Bastardkb/Charybdis/pics/1aa.png

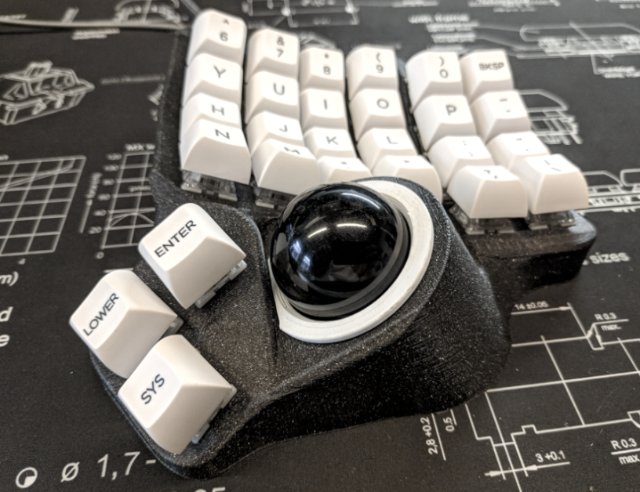
pics/1aa.png
