Bastardkb/Charybdis/pics/1ab.jpeg

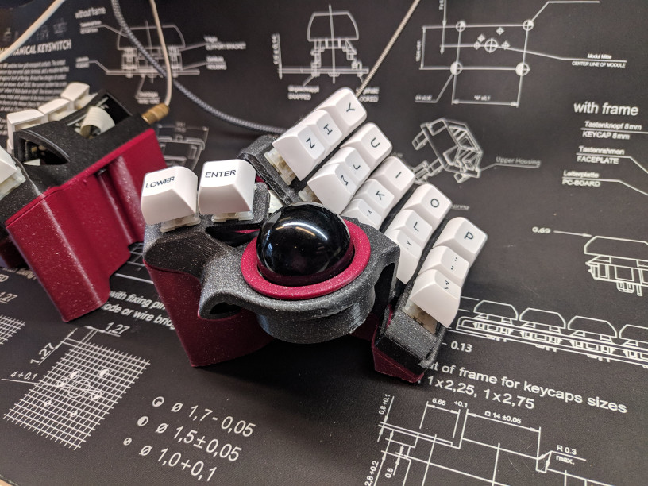
pics/1ab.jpeg
