Bastardkb/Charybdis/pics/1af.jpg

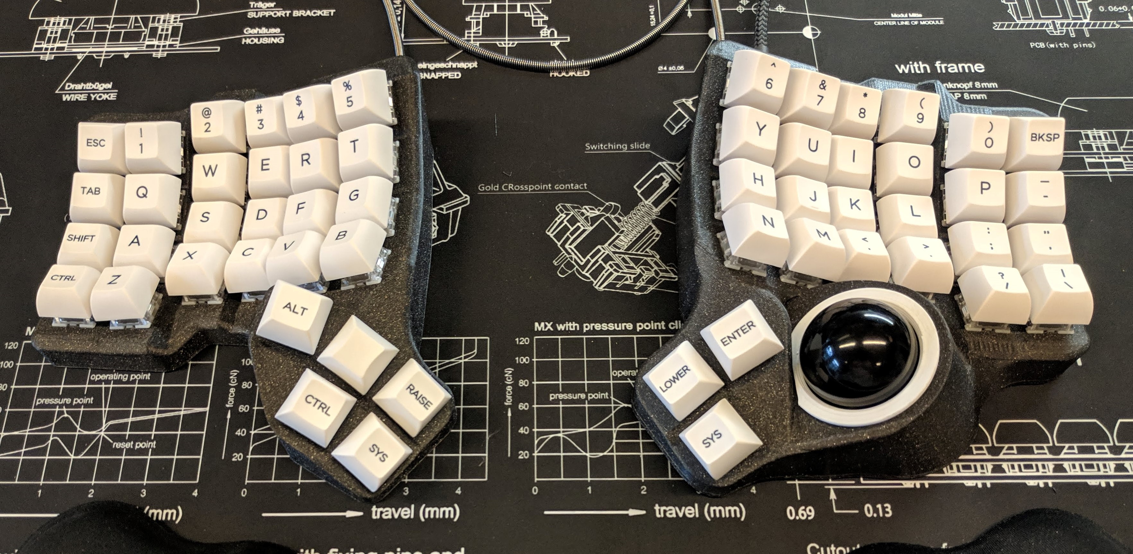
pics/1af.jpg
