Bastardkb/Charybdis/files/adapter_v4_bottom_v17.stl

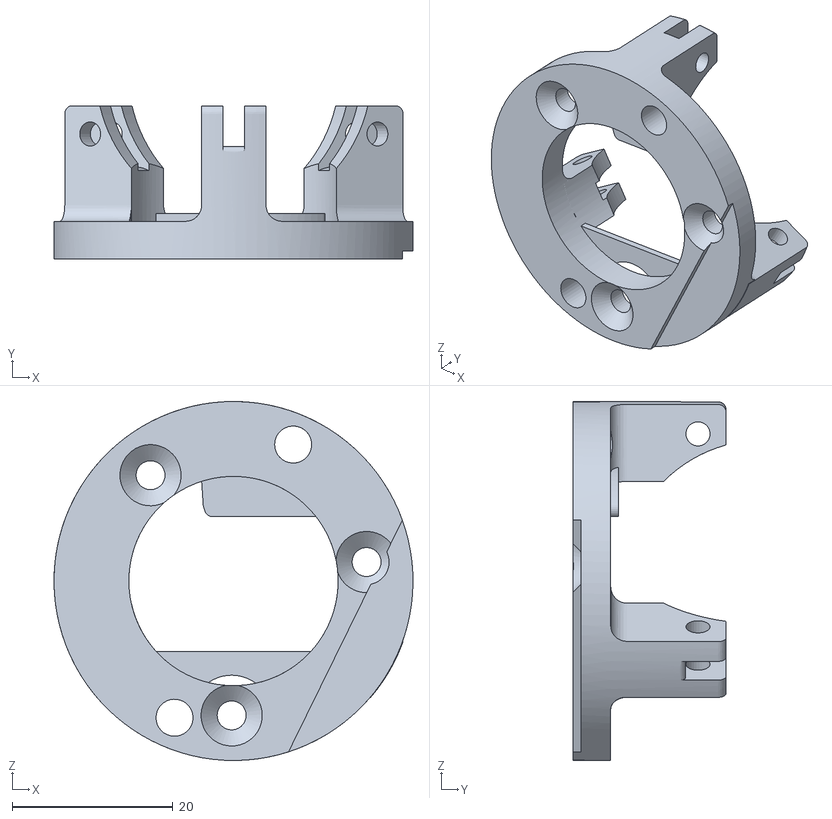
[picture p79: CAD file, 2023-07-04]
files/adapter_v4_bottom_v17.stl
44.6 x 19.1 x 44.6
