Bastardkb/Charybdis/files/mods/4x6-palm-rest-mkII/charybdis_v4_247_right_with_pads.stl

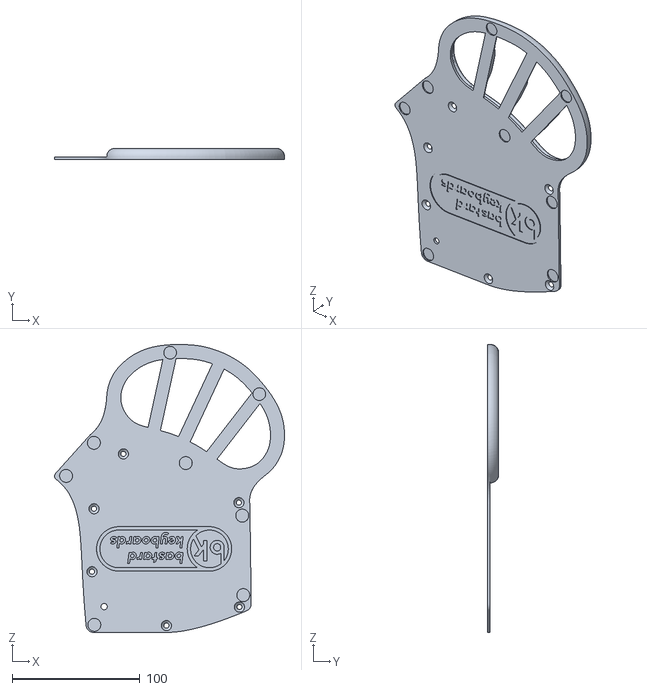
[picture p80: CAD file, 2025-02-24]
files/mods/4x6-palm-rest-mkII/charybdis_v4_247_right_with_pads.stl
180.3 x 9.00 x 225.7
