Bastardkb/Charybdis/files/mods/4x6-palm-rest/Charybdis-PlamRest-Straight.SLDPRT

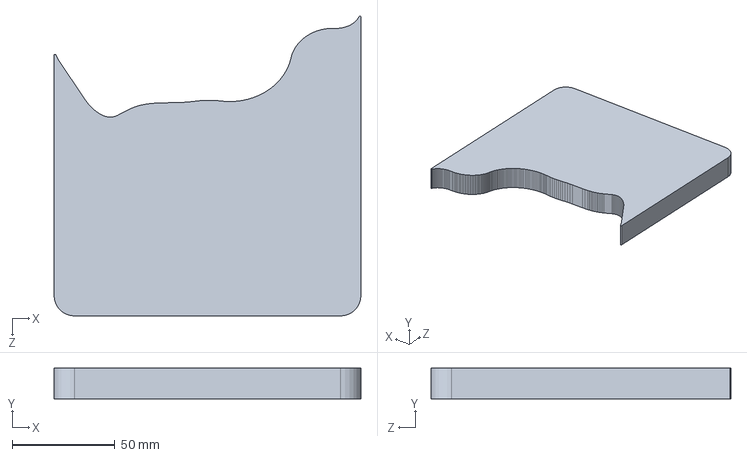
[picture p81: CAD file, 2023-12-05]
files/mods/4x6-palm-rest/Charybdis-PlamRest-Straight.SLDPRT
149.6 x 15.0 x 146.2 mm
