Bastardkb/Charybdis/files/mods/aa_3.7v_battery_holder/battery_holder_cover.stl

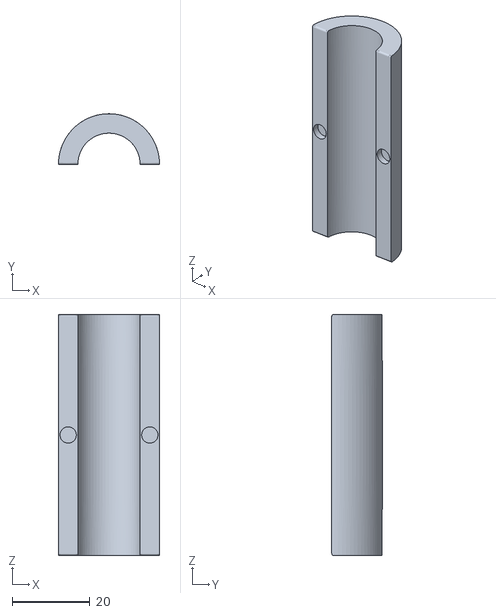
[picture p82: CAD file, 2025-08-21]
files/mods/aa_3.7v_battery_holder/battery_holder_cover.stl
26.0 x 13.0 x 62.0
