Bastardkb/Charybdis/files/mods/aa_3.7v_battery_holder/charybdis_mini/TBK_mini_v3 v29_snap_fit_with_battery.stl

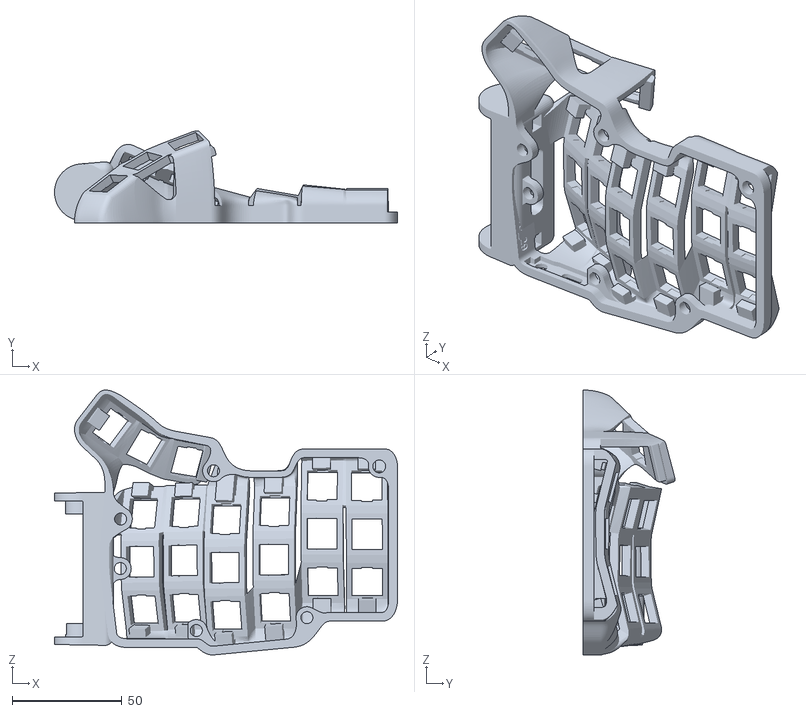
[picture p83: CAD file, 2025-08-21]
files/mods/aa_3.7v_battery_holder/charybdis_mini/TBK_mini_v3 v29_snap_fit_with_battery.stl
156.5 x 42.0 x 120.9
