Bastardkb/Charybdis/files/mods/aa_3.7v_battery_holder/charybdis_nano/charybdisnano_v2_v187_snap_fit_with_battery.stl

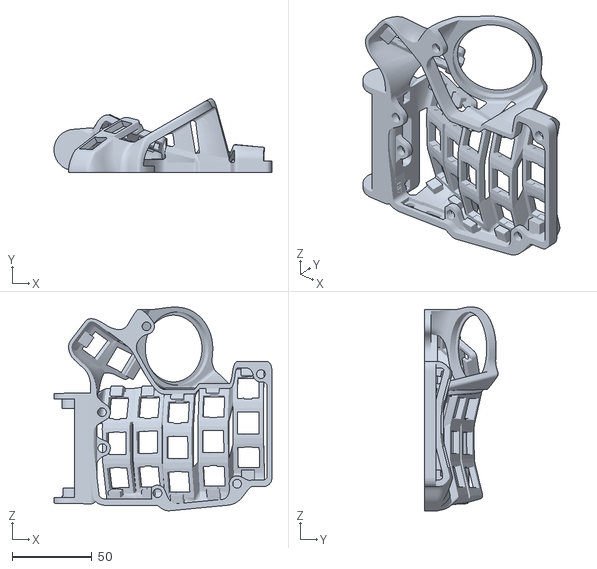
[picture p84: CAD file, 2025-08-21]
files/mods/aa_3.7v_battery_holder/charybdis_nano/charybdisnano_v2_v187_snap_fit_with_battery.stl
137.1 x 46.2 x 128.1
