Bastardkb/Charybdis/files/mods/bottom_adapter_alternative_sensors/adapter_paw3360_3389_module_20240424.stl

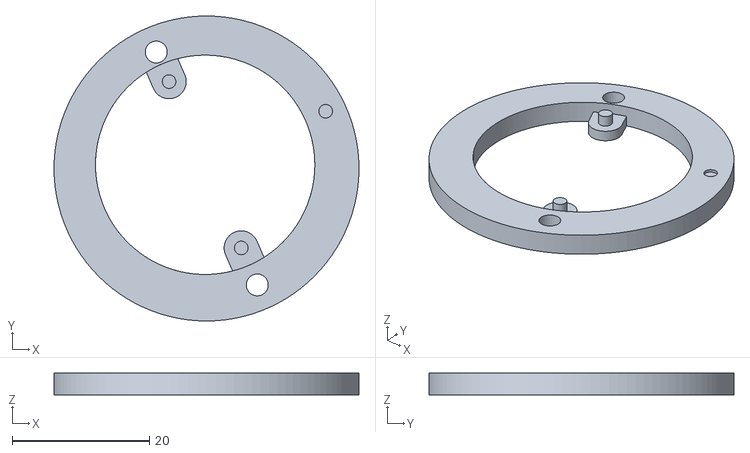
[picture p85: CAD file, 2026-08-29]
files/mods/bottom_adapter_alternative_sensors/adapter_paw3360_3389_module_20240424.stl
44.5 x 44.5 x 3.20
