Bastardkb/Charybdis/files/mods/btu/adapter_btu_bottom_v32.stl

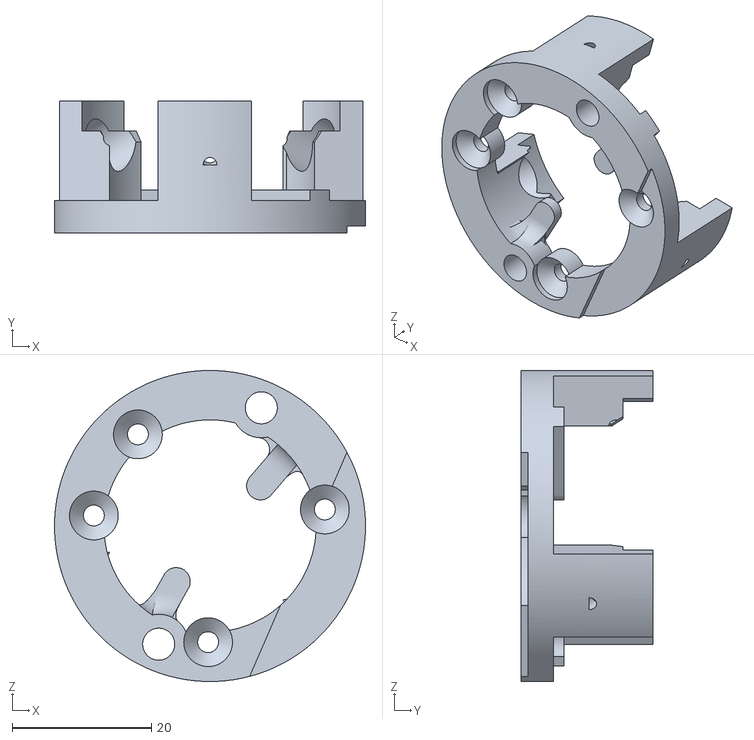
[picture p86: CAD file, 2021-10-12]
files/mods/btu/adapter_btu_bottom_v32.stl
44.7 x 19.0 x 44.7
