Bastardkb/Charybdis/files/mods/modular-thumb-cluster/mod-case.stl

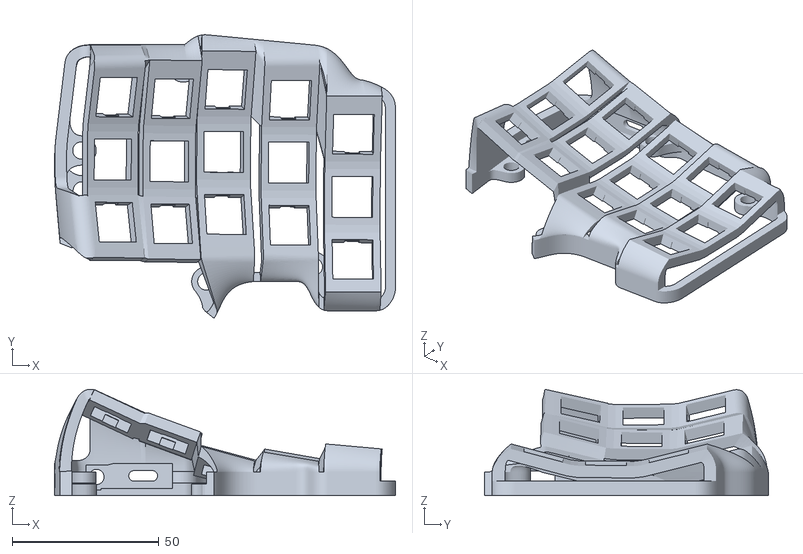
[picture p87: CAD file, 2022-09-18]
files/mods/modular-thumb-cluster/mod-case.stl
116.1 x 96.5 x 36.2
