Bastardkb/Charybdis/files/mods/pg1353_choc_v2/3x5_3_high_v2_pg1353_left.3mf

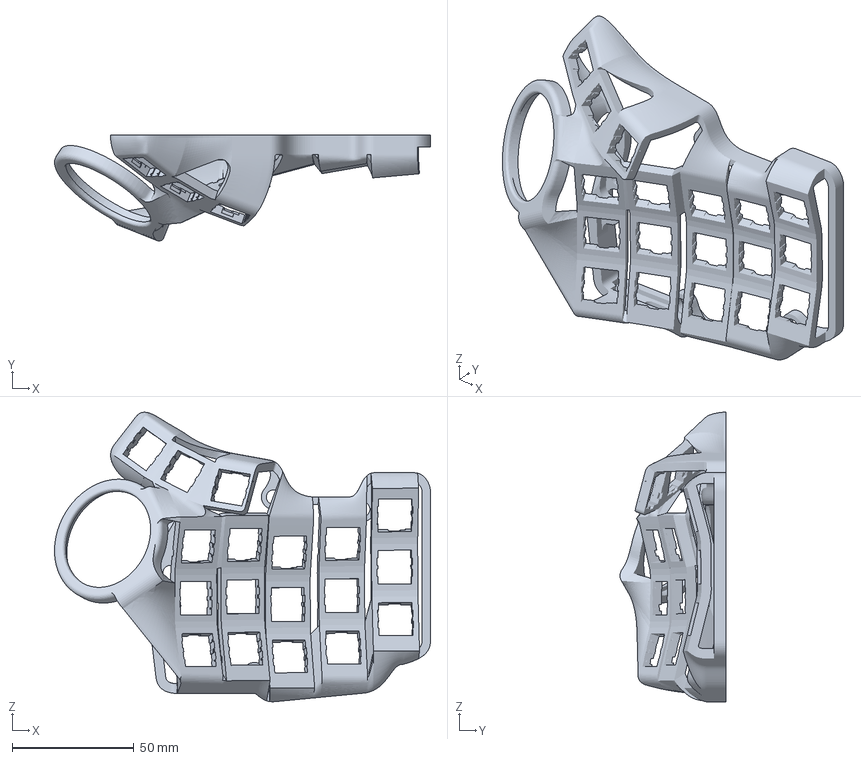
[picture p88: CAD file, 2026-08-30]
files/mods/pg1353_choc_v2/3x5_3_high_v2_pg1353_left.3mf
154.3 x 43.5 x 118.8 mm
