Bastardkb/Charybdis/files/mods/sensor_cover/Sensor_cover.stl

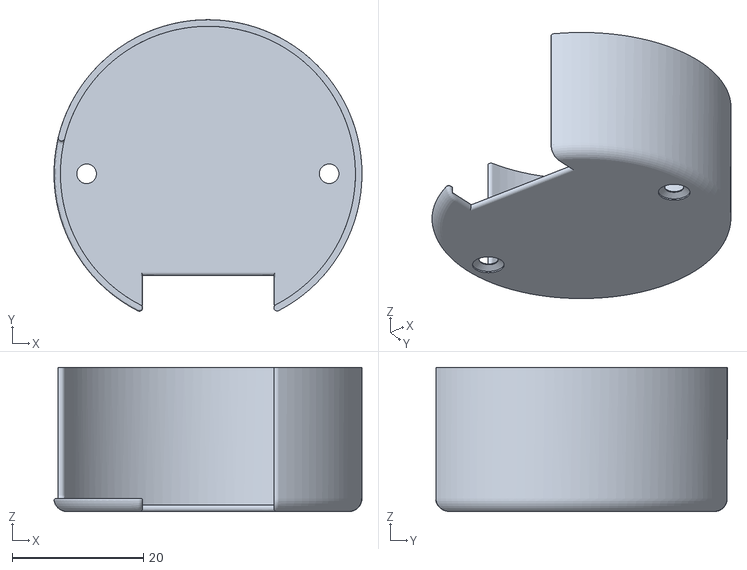
[picture p89: CAD file, 2023-04-05]
files/mods/sensor_cover/Sensor_cover.stl
47.0 x 44.5 x 22.0
