Bastardkb/Charybdis/files/mods/snapfit_pcb_case/charybdis_mini/CMini_v1_v11_snap_fit.stl

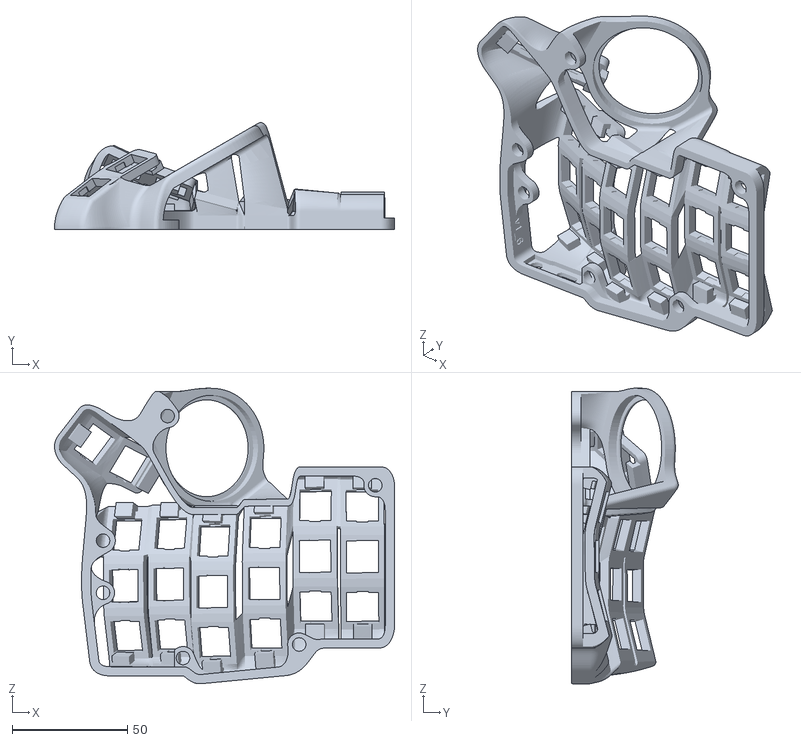
[picture p90: CAD file, 2025-08-21]
files/mods/snapfit_pcb_case/charybdis_mini/CMini_v1_v11_snap_fit.stl
147.4 x 46.2 x 128.1
