Bastardkb/Charybdis/files/mods/snapfit_pcb_case/charybdis_nano/charybdisnano_v2_v187_snap_fit.stl

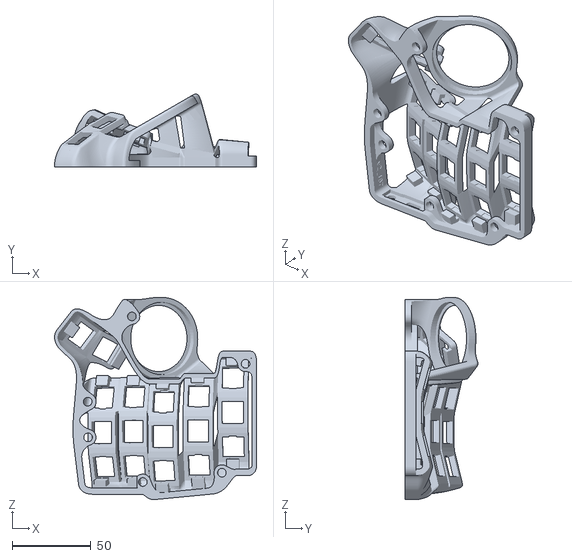
[picture p91: CAD file, 2025-08-21]
files/mods/snapfit_pcb_case/charybdis_nano/charybdisnano_v2_v187_snap_fit.stl
128.0 x 46.2 x 128.1
