Bastardkb/Charybdis/files/mods/Static-bearing-Veichu-drop-in/Static-bearing-holder_v221117.stl

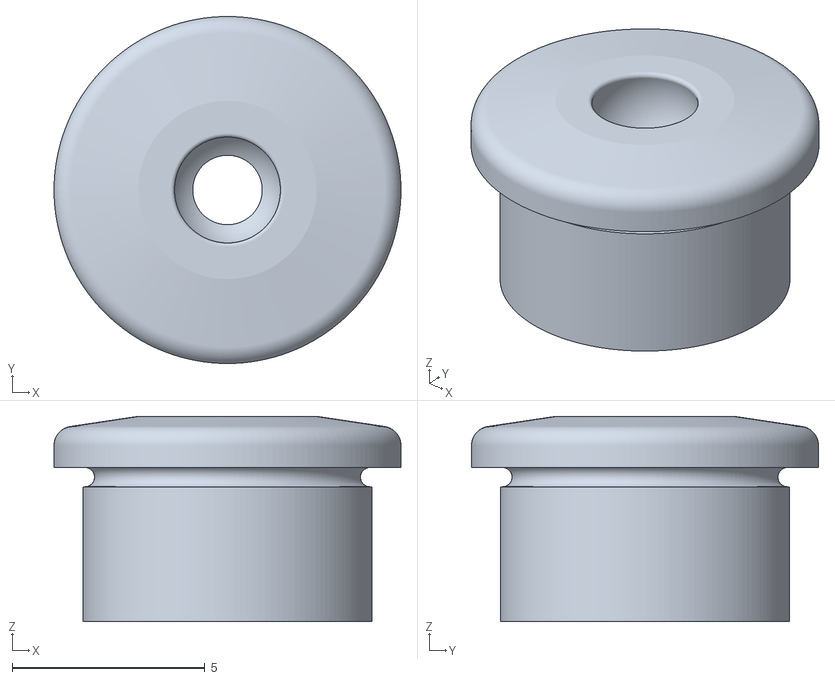
[picture p92: CAD file, 2024-09-02]
files/mods/Static-bearing-Veichu-drop-in/Static-bearing-holder_v221117.stl
9.00 x 9.00 x 5.33
