Bastardkb/Charybdis/files/mods/static-bearing/printable_btu_2.5mm_ball.stl

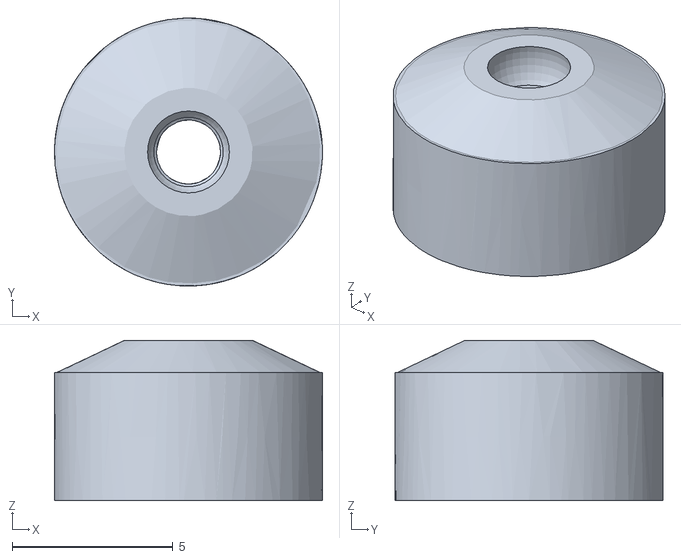
[picture p93: CAD file, 2022-09-18]
files/mods/static-bearing/printable_btu_2.5mm_ball.stl
8.35 x 8.35 x 5.00
