Bastardkb/Charybdis/files/mods/tenting-stand-with-wrist-pads/3x5+3_low_tent_plate.stl

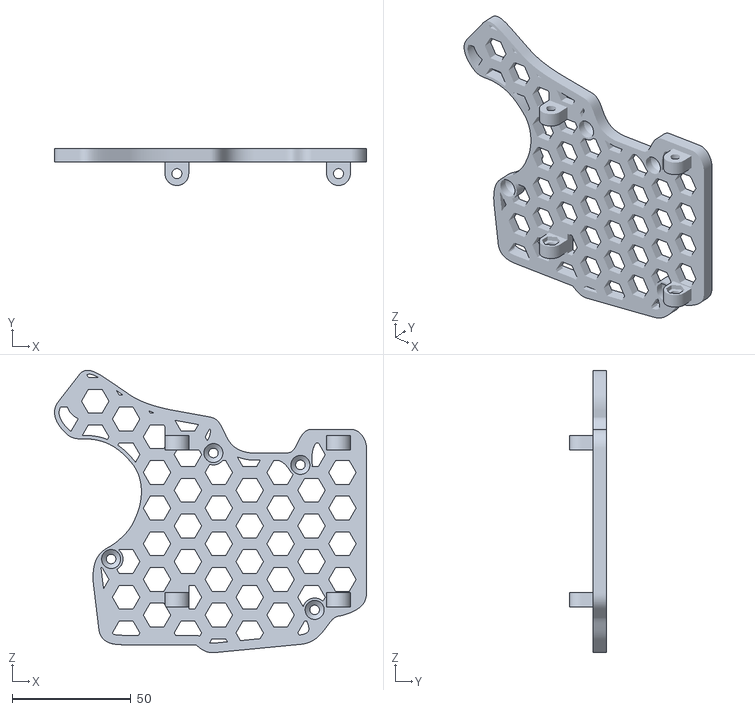
[picture p94: CAD file, 2023-08-22]
files/mods/tenting-stand-with-wrist-pads/3x5+3_low_tent_plate.stl
131.3 x 15.6 x 118.8
