Bastardkb/Charybdis/files/mods/tenting-stand-with-wrist-pads/wrist-pad-variant-parts/pads-base-short.stl

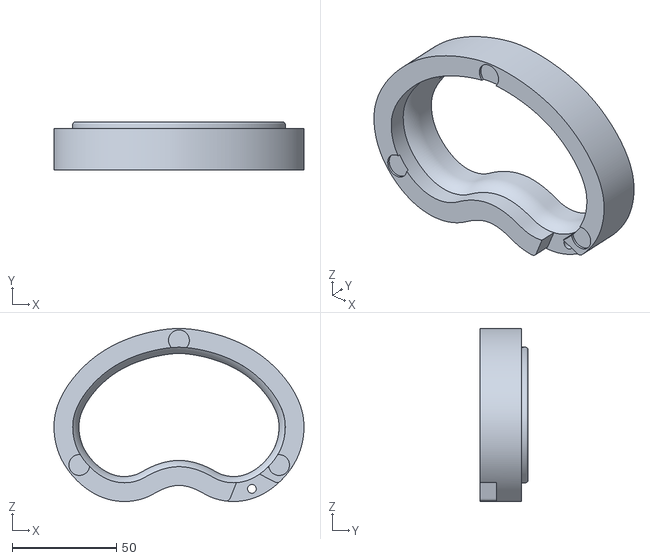
[picture p95: CAD file, 2023-08-22]
files/mods/tenting-stand-with-wrist-pads/wrist-pad-variant-parts/pads-base-short.stl
120.0 x 23.0 x 83.1
