Bastardkb/Charybdis/files/mods/trackball_retainer/3x5/Ball_cover_resin_5mm.stl

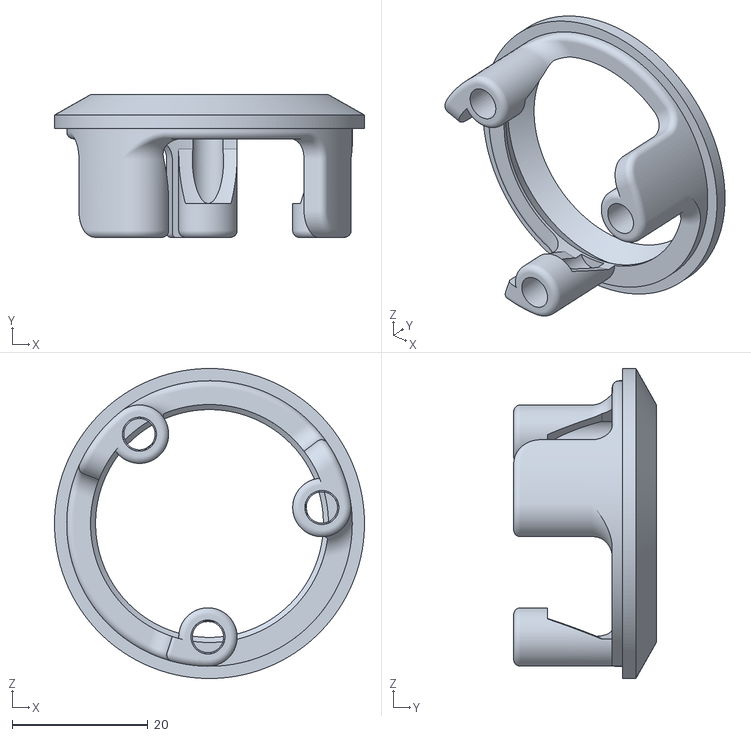
[picture p96: CAD file, 2024-01-04]
files/mods/trackball_retainer/3x5/Ball_cover_resin_5mm.stl
45.6 x 21.0 x 45.6
