Bastardkb/Charybdis/files/mods/trackball_retainer/4x6/trackball_retainer.stl

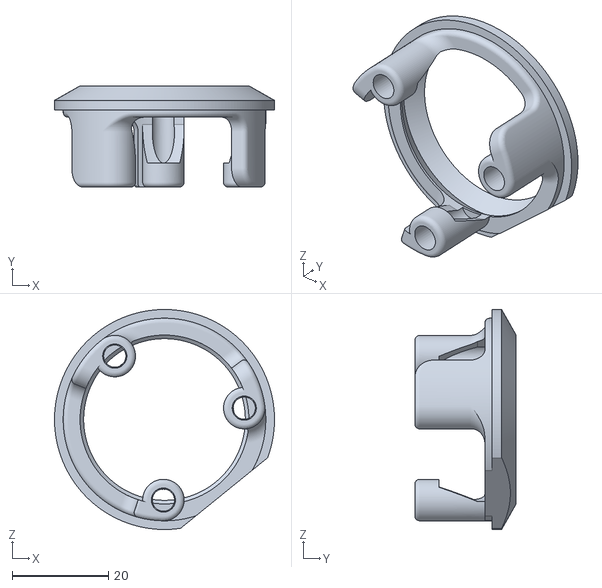
[picture p97: CAD file, 2025-02-24]
files/mods/trackball_retainer/4x6/trackball_retainer.stl
45.6 x 21.0 x 45.6
