Bastardkb/Charybdis/files/mods/trackpad/3x5-tent/tent-connector.stl

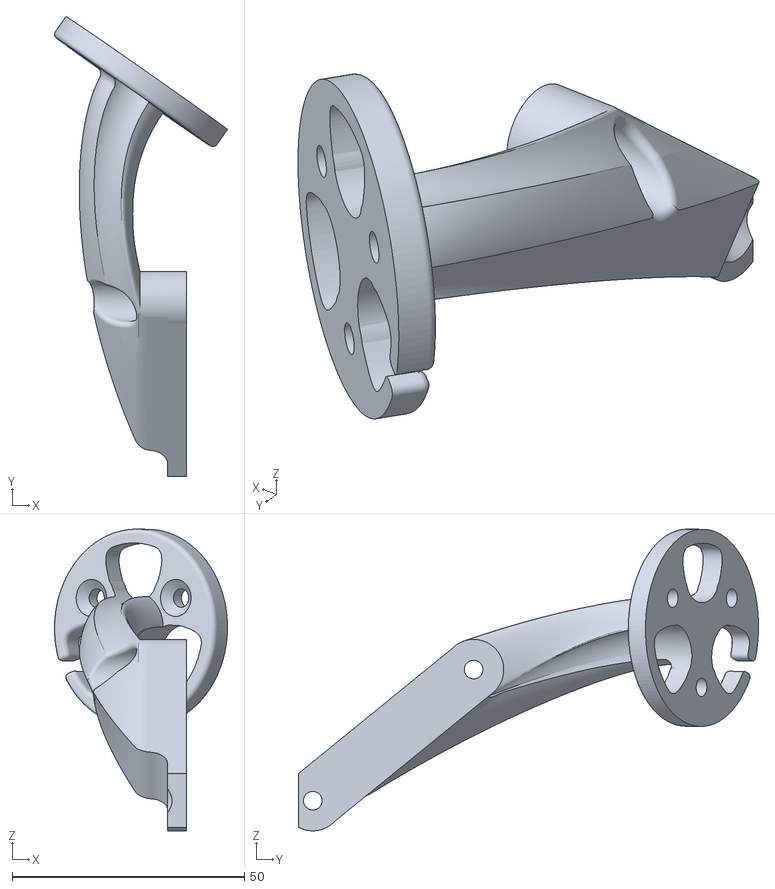
[picture p98: CAD file, 2022-04-11]
files/mods/trackpad/3x5-tent/tent-connector.stl
37.3 x 99.1 x 65.0
