Bastardkb/Charybdis/files/mods/trackpad/trackball-holder/bot.stl

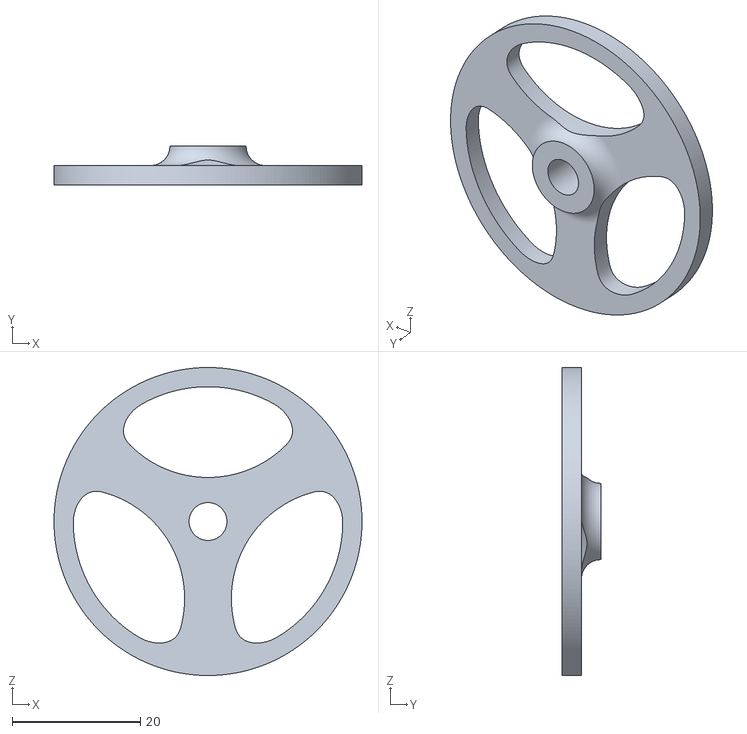
[picture p99: CAD file, 2022-05-02]
files/mods/trackpad/trackball-holder/bot.stl
48.0 x 6.00 x 48.0
