Bastardkb/Charybdis/files/mods/veichu/veichu.stl

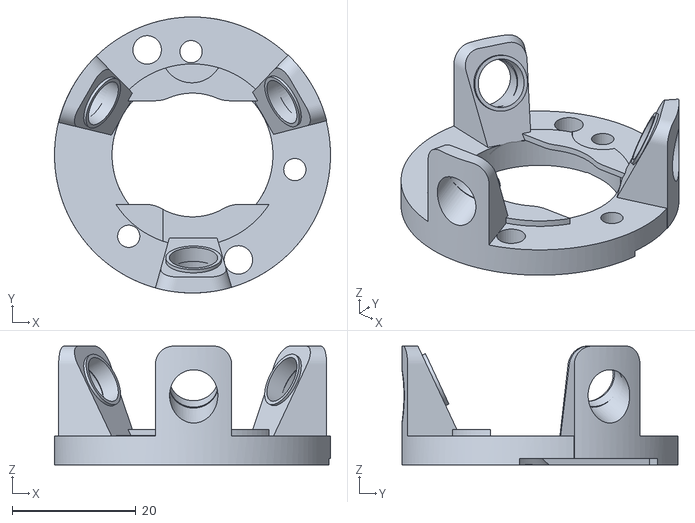
[picture p100: CAD file, 2024-06-24]
files/mods/veichu/veichu.stl
44.6 x 44.6 x 19.2
