Bastardkb/Charybdis/files/3x5 nano/adapter_v2_top_v75.stl

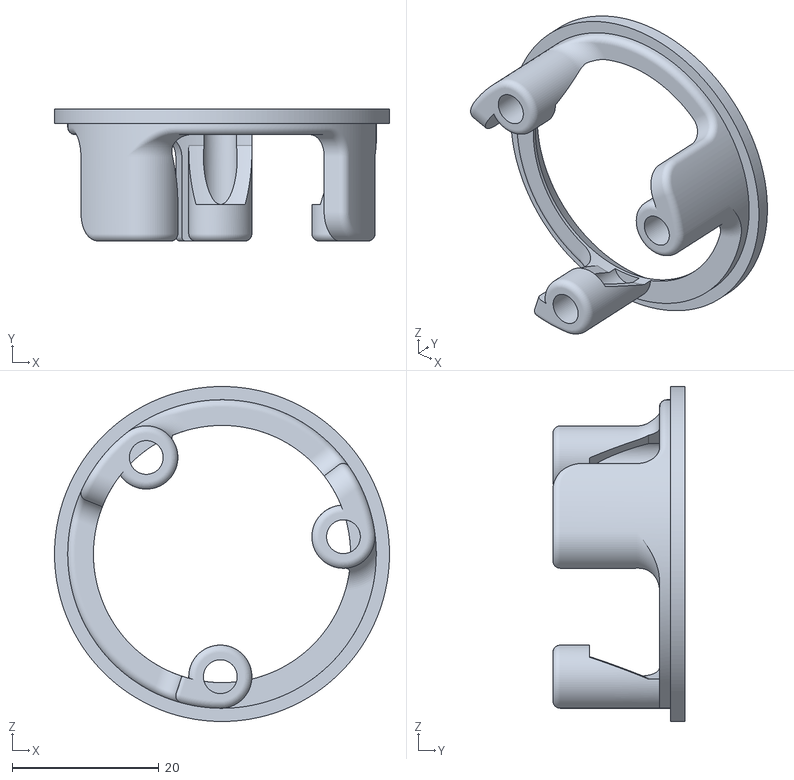
[picture p101: CAD file, 2022-05-30]
files/3x5 nano/adapter_v2_top_v75.stl
45.6 x 18.0 x 45.6
