Bastardkb/Charybdis/files/3x5 nano/magnetic system/magtent.stl

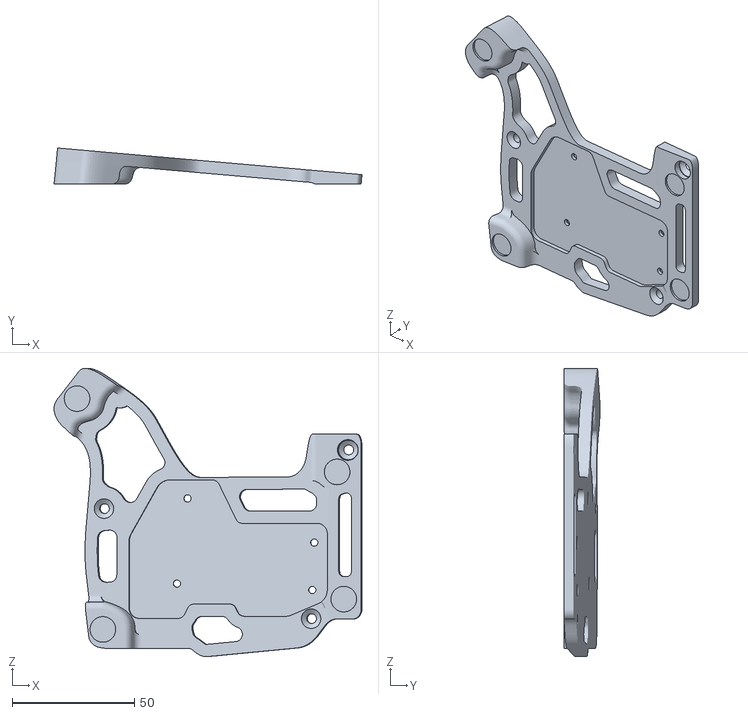
[picture p102: CAD file, 2026-03-30]
files/3x5 nano/magnetic system/magtent.stl
125.9 x 14.7 x 117.9
