Bastardkb/Charybdis/files/3x5 nano/plates/magsafe_3dp_v0_1.stl

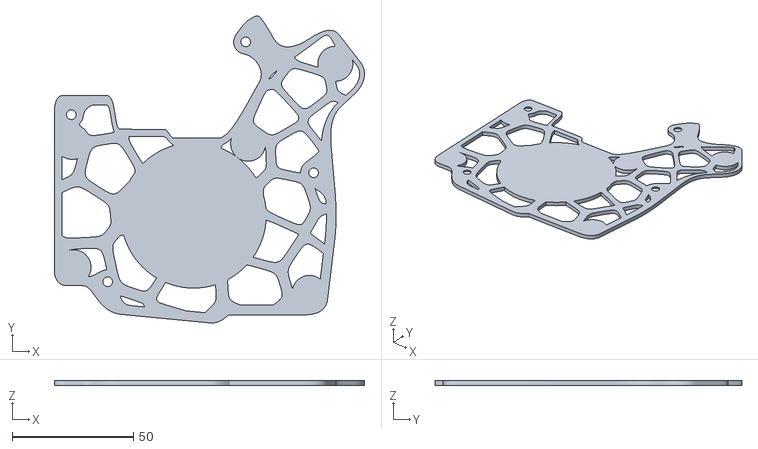
[picture p103: CAD file, 2023-12-04]
files/3x5 nano/plates/magsafe_3dp_v0_1.stl
128.0 x 126.7 x 2.00
