Bastardkb/Charybdis/files/3x5 nano/tent/alien/tent_flush_v8_1.stl

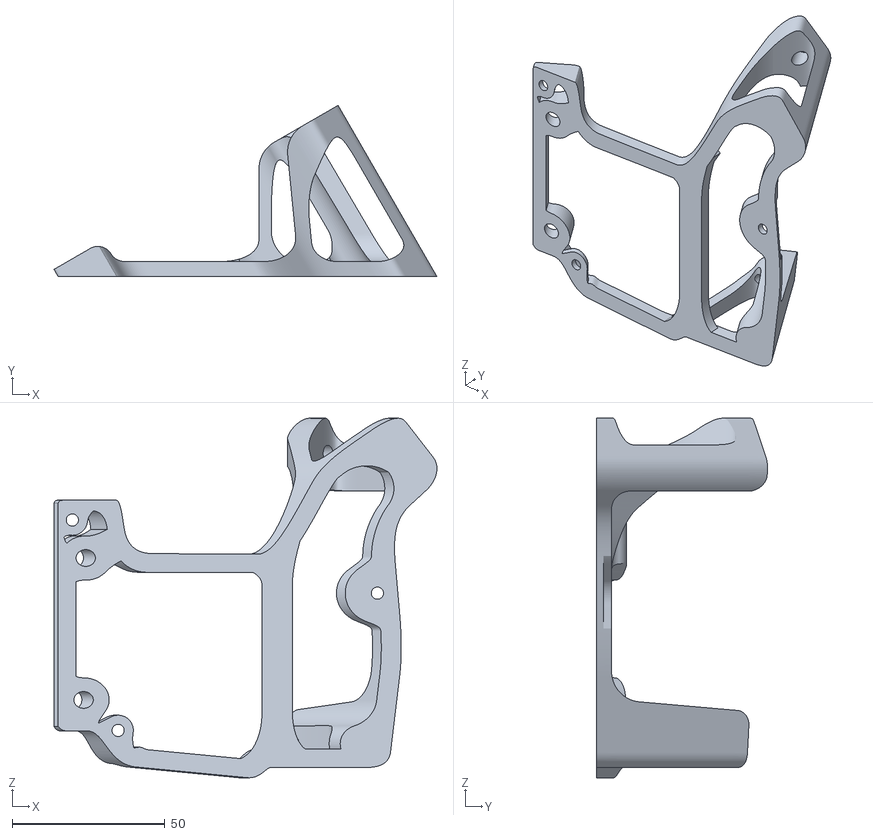
[picture p104: CAD file, 2025-02-20]
files/3x5 nano/tent/alien/tent_flush_v8_1.stl
125.6 x 56.2 x 117.9
