Bastardkb/Charybdis/files/3x5 nano/tent/normal/tent30deg_v1_4.stl

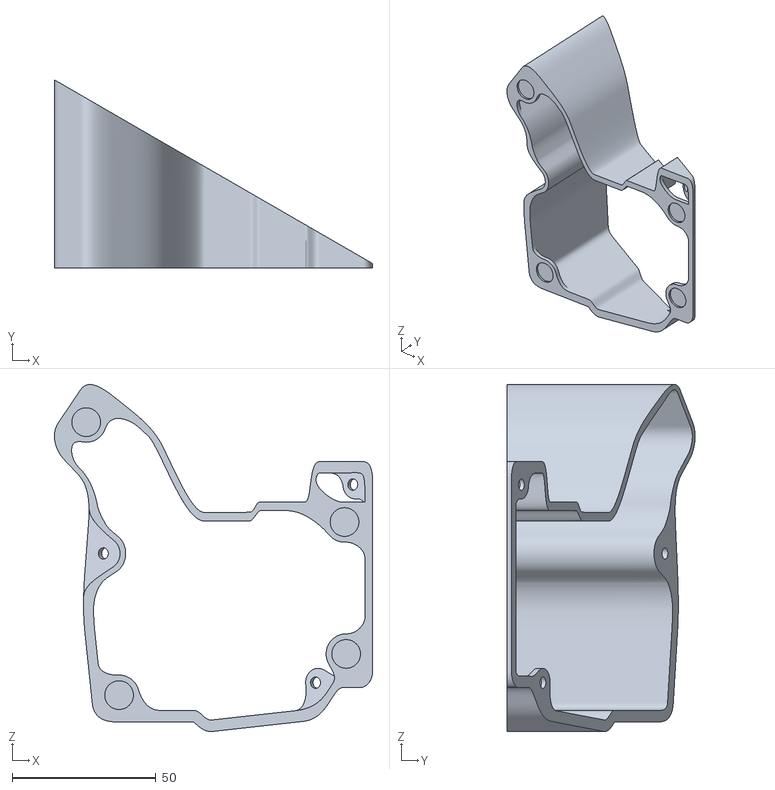
[picture p105: CAD file, 2021-08-09]
files/3x5 nano/tent/normal/tent30deg_v1_4.stl
110.8 x 65.6 x 120.9
