Bastardkb/Charybdis/files/3x5 nano/tent/organic/plate_v1_41.stl

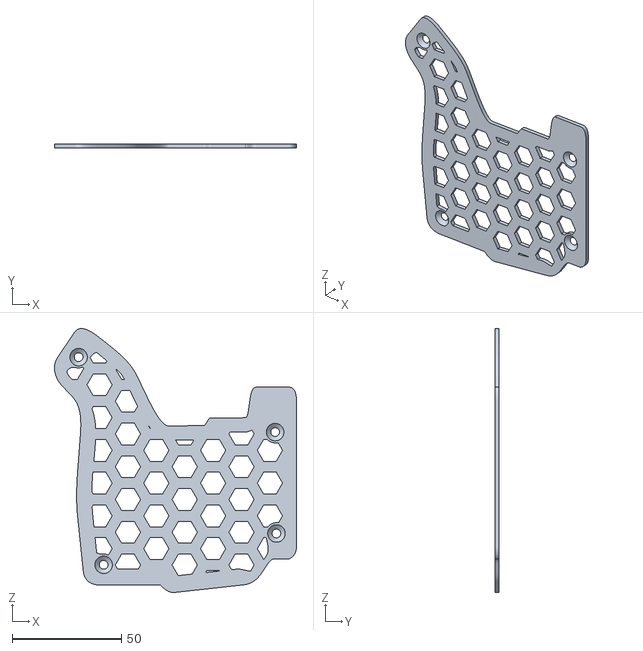
[picture p106: CAD file, 2022-01-12]
files/3x5 nano/tent/organic/plate_v1_41.stl
110.8 x 2.00 x 120.9
