Bastardkb/Charybdis/files/3x5+3/HighTrackball/3x5_3 high v2.stl

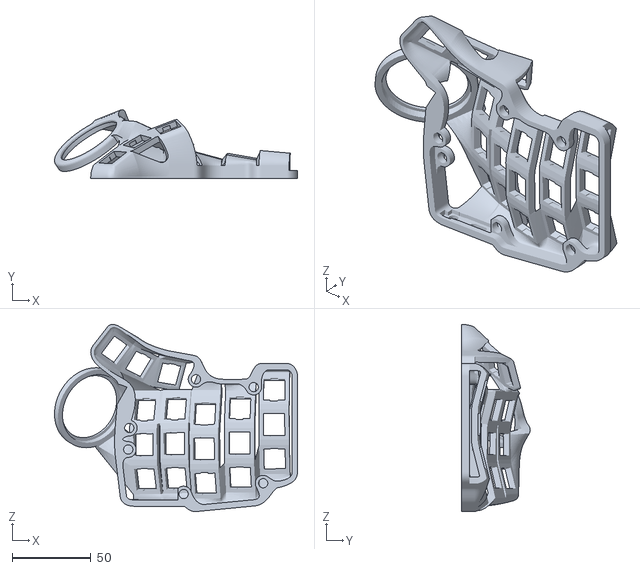
[picture p107: CAD file, 2022-06-27]
files/3x5+3/HighTrackball/3x5_3 high v2.stl
154.3 x 43.5 x 118.8
