Bastardkb/Charybdis/files/3x5+3/LowTrackball/3x5+3_low_clipped.stl

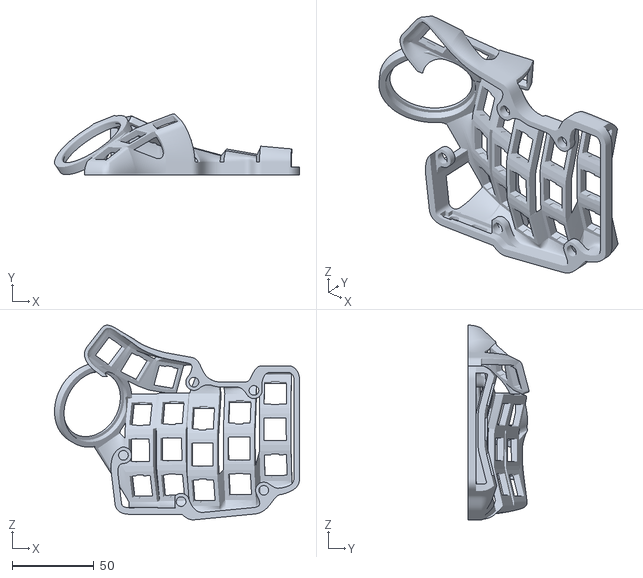
[picture p108: CAD file, 2023-08-22]
files/3x5+3/LowTrackball/3x5+3_low_clipped.stl
149.5 x 37.3 x 118.8
