Bastardkb/Charybdis/files/3x5+3/MountedMods/TopEncoderMod v6.stl

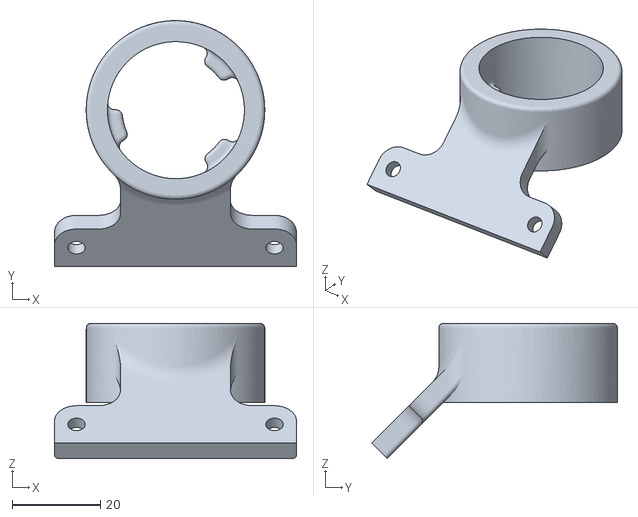
[picture p109: CAD file, 2022-09-18]
files/3x5+3/MountedMods/TopEncoderMod v6.stl
55.0 x 55.9 x 30.7
