Bastardkb/Charybdis/files/3x6 mini/plate_flush_v1_v1.stl

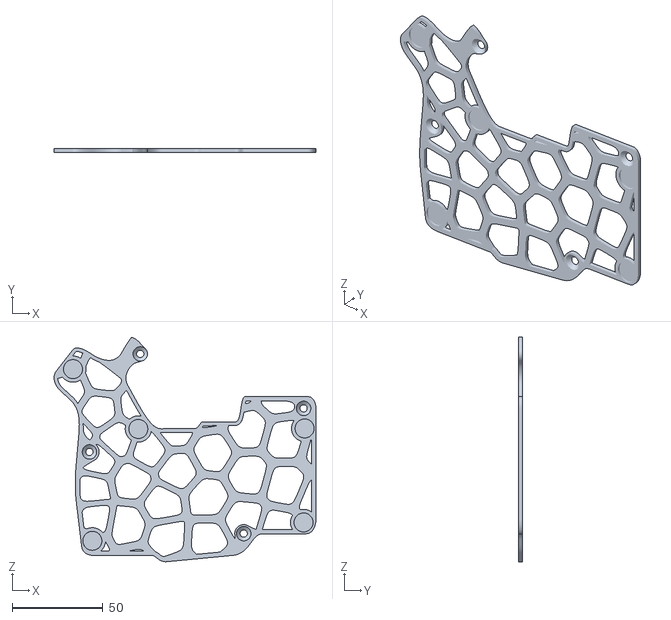
[picture p110: CAD file, 2025-03-21]
files/3x6 mini/plate_flush_v1_v1.stl
144.4 x 2.00 x 123.7
