Bastardkb/Charybdis/files/4x6/MK2/tent_alien_30deg_v3_11.stl

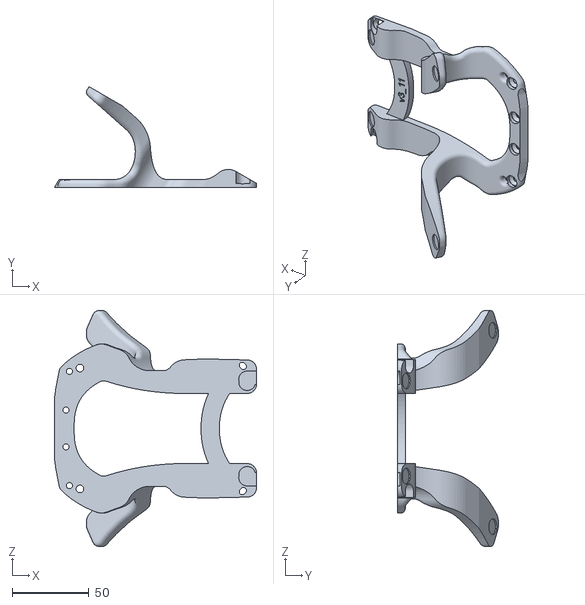
[picture p111: CAD file, 2025-08-12]
files/4x6/MK2/tent_alien_30deg_v3_11.stl
131.9 x 65.8 x 154.1
