Bastardkb/Charybdis/files/mods/4x6-palm-rest/Charybdis-PlamRest-Slope.SLDPRT

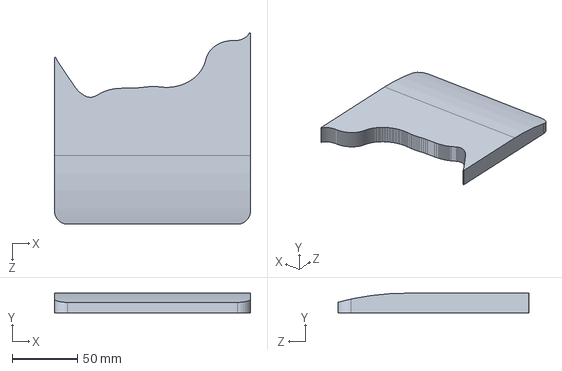
[picture p112: CAD file, 2023-12-05]
files/mods/4x6-palm-rest/Charybdis-PlamRest-Slope.SLDPRT
149.6 x 15.0 x 146.2 mm
