Bastardkb/Charybdis/files/mods/aa_3.7v_battery_holder/charybdis_mini/CMini_v1_v11_snap_fit_with_battery.stl

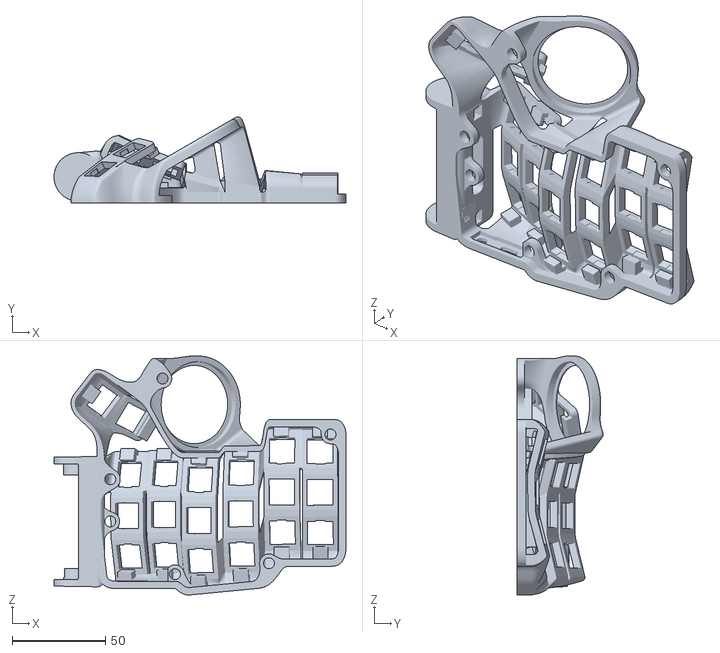
[picture p113: CAD file, 2025-08-21]
files/mods/aa_3.7v_battery_holder/charybdis_mini/CMini_v1_v11_snap_fit_with_battery.stl
156.5 x 46.2 x 128.1
