Bastardkb/Charybdis/files/mods/aa_3.7v_battery_holder/charybdis_nano/Skeletyl_case_v4_v99_snap_fit_with_battery.stl

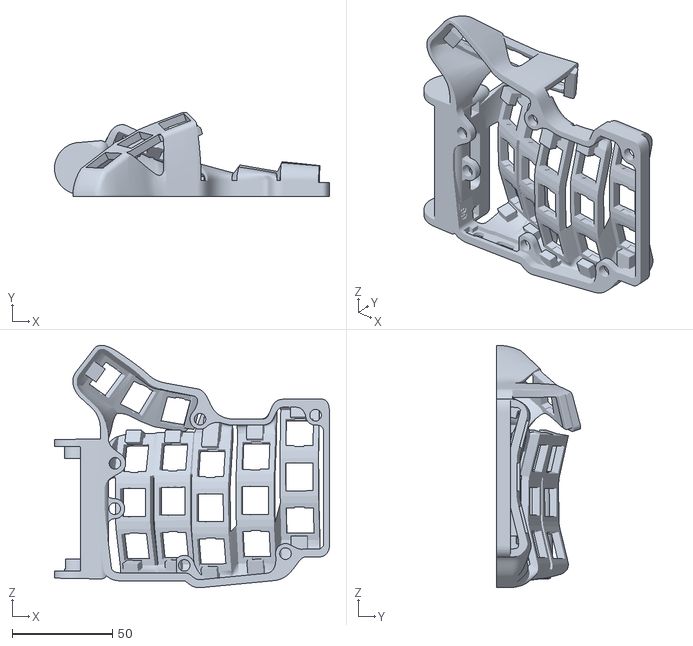
[picture p114: CAD file, 2025-08-21]
files/mods/aa_3.7v_battery_holder/charybdis_nano/Skeletyl_case_v4_v99_snap_fit_with_battery.stl
137.1 x 42.0 x 120.9
