Bastardkb/Charybdis/files/mods/bottom_adapter_alternative_sensors/adapter_v2_bottom_adns_9800.stl

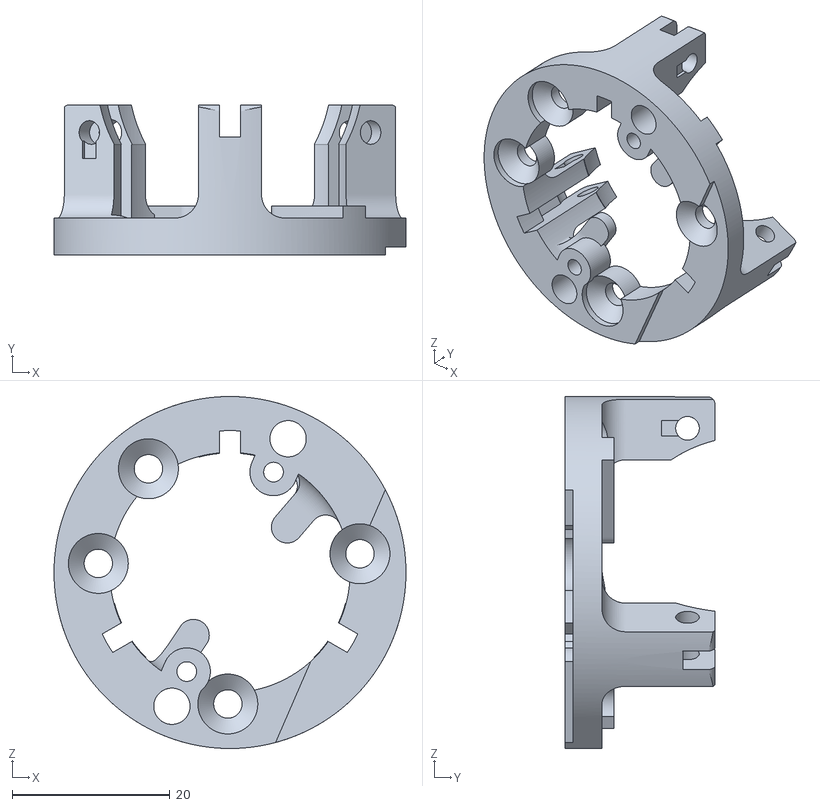
[picture p115: CAD file, 2023-08-22]
files/mods/bottom_adapter_alternative_sensors/adapter_v2_bottom_adns_9800.stl
44.7 x 19.1 x 44.7
