Bastardkb/Charybdis/files/mods/modular-thumb-cluster/NewPlate.stl

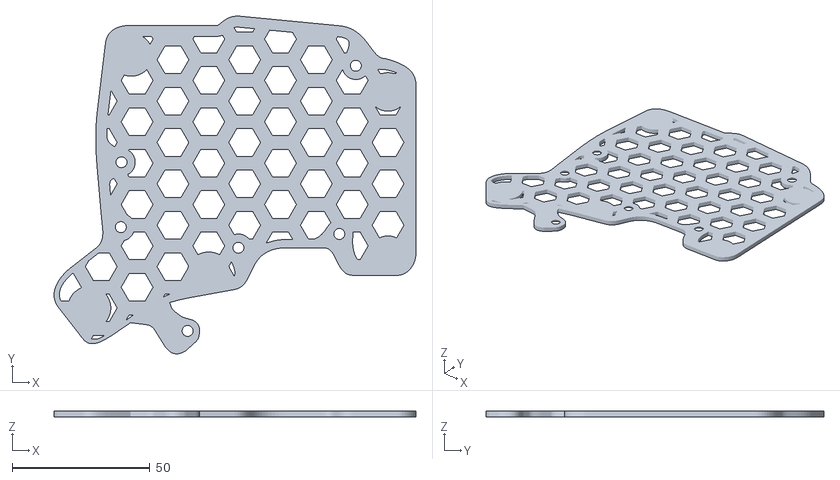
[picture p116: CAD file, 2022-09-18]
files/mods/modular-thumb-cluster/NewPlate.stl
131.3 x 122.5 x 2.00
