Bastardkb/Charybdis/files/mods/snapfit_pcb_case/charybdis_mini/TBK_mini_v3 v29_snap_fit.stl

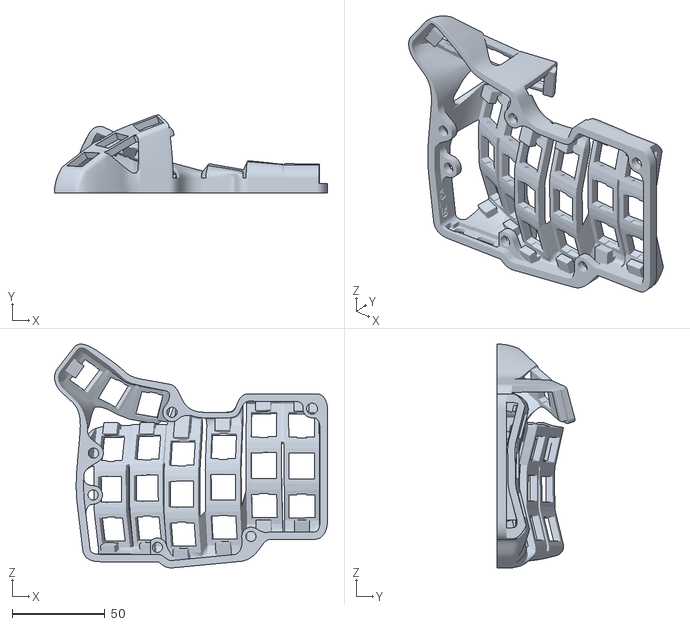
[picture p117: CAD file, 2025-08-21]
files/mods/snapfit_pcb_case/charybdis_mini/TBK_mini_v3 v29_snap_fit.stl
147.4 x 42.0 x 120.9
