Bastardkb/Charybdis/files/mods/snapfit_pcb_case/charybdis_nano/skeletyl_v4_v99_snap_fit.stl

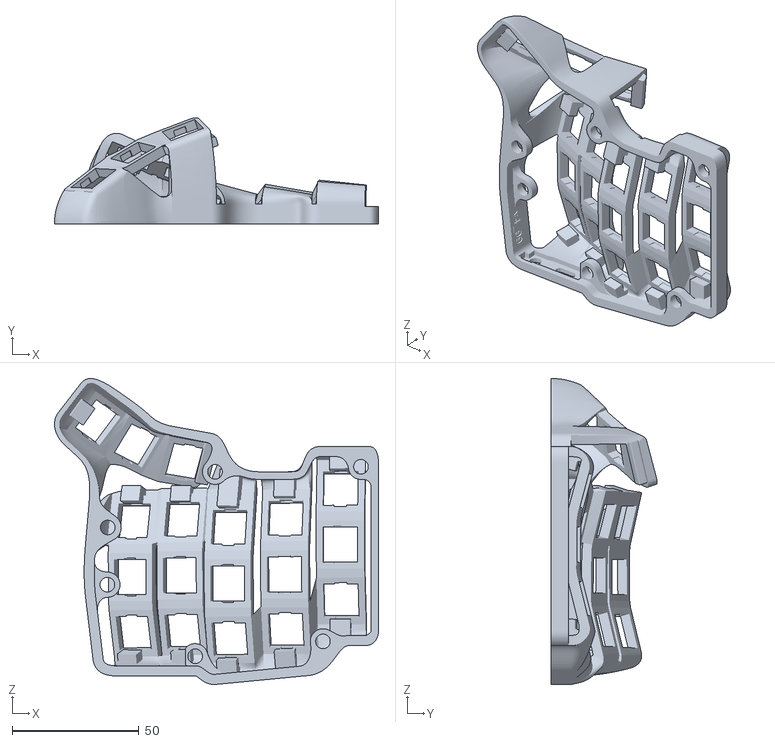
[picture p118: CAD file, 2025-08-21]
files/mods/snapfit_pcb_case/charybdis_nano/skeletyl_v4_v99_snap_fit.stl
128.0 x 42.0 x 120.9
