Bastardkb/Charybdis/files/mods/static-bearing/printable_btu_3.175mm_ball.stl

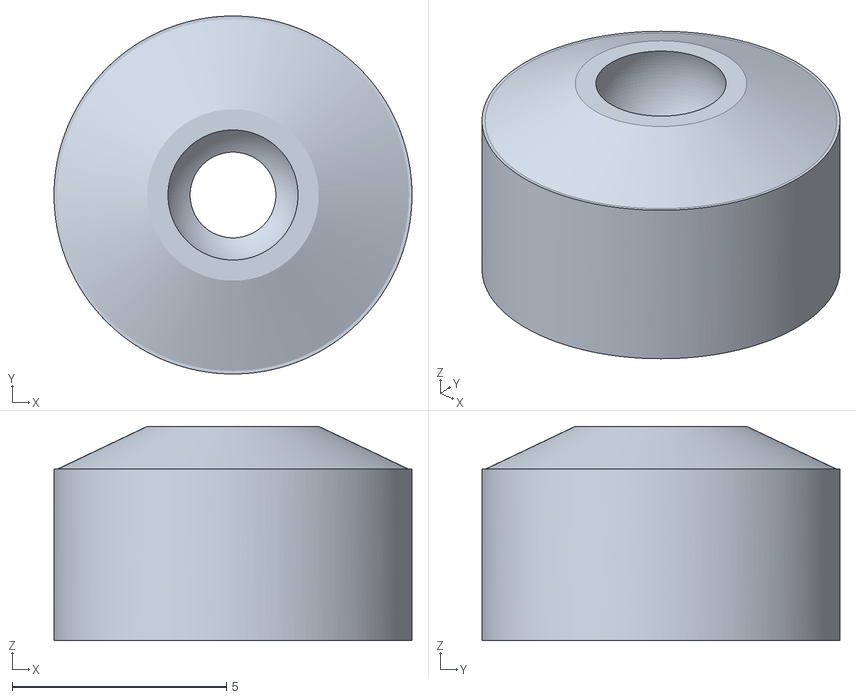
[picture p119: CAD file, 2021-11-30]
files/mods/static-bearing/printable_btu_3.175mm_ball.stl
8.35 x 8.35 x 5.00
