Bastardkb/Charybdis/files/mods/tenting-stand-with-wrist-pads/right-case-bottom-charybdis.3mf

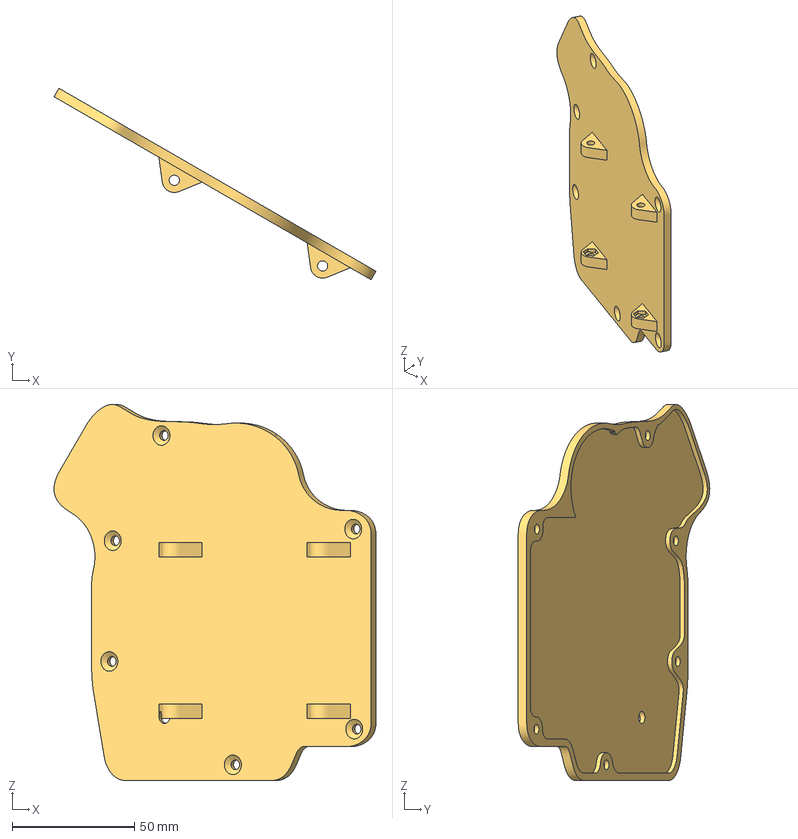
[picture p120: CAD file, 2022-11-10]
files/mods/tenting-stand-with-wrist-pads/right-case-bottom-charybdis.3mf
131.6 x 78.3 x 153.7 mm
