Bastardkb/Charybdis/files/mods/tenting-stand-with-wrist-pads/wrist-pad-variant-parts/pads-arm-extended.stl

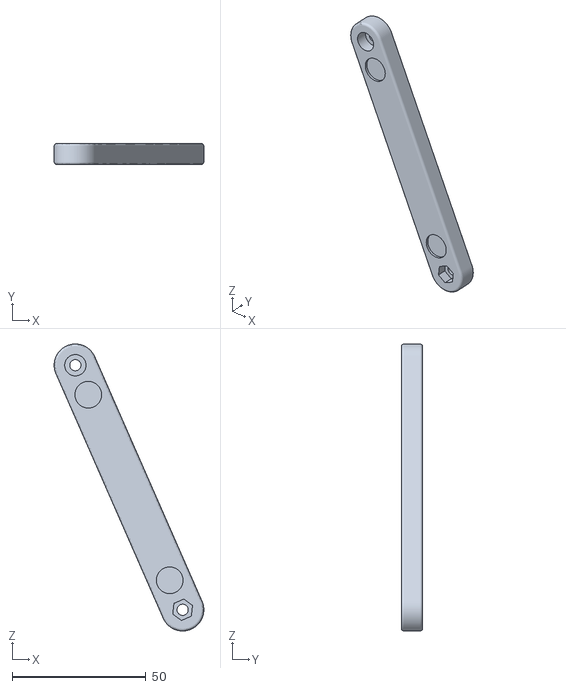
[picture p121: CAD file, 2023-08-22]
files/mods/tenting-stand-with-wrist-pads/wrist-pad-variant-parts/pads-arm-extended.stl
56.1 x 8.00 x 107.5
