Bastardkb/Charybdis/files/mods/trackpad/3x5-tent/trackpad-holder.stl

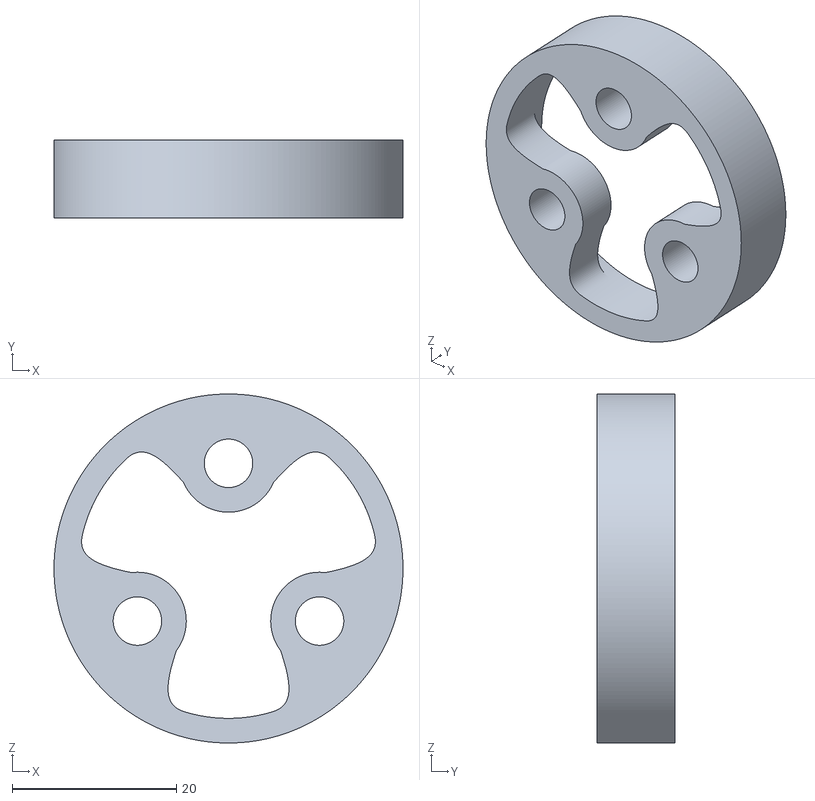
[picture p122: CAD file, 2022-04-11]
files/mods/trackpad/3x5-tent/trackpad-holder.stl
42.5 x 9.50 x 42.5
