Bastardkb/Charybdis/files/mods/trackpad/trackball-holder/top.stl

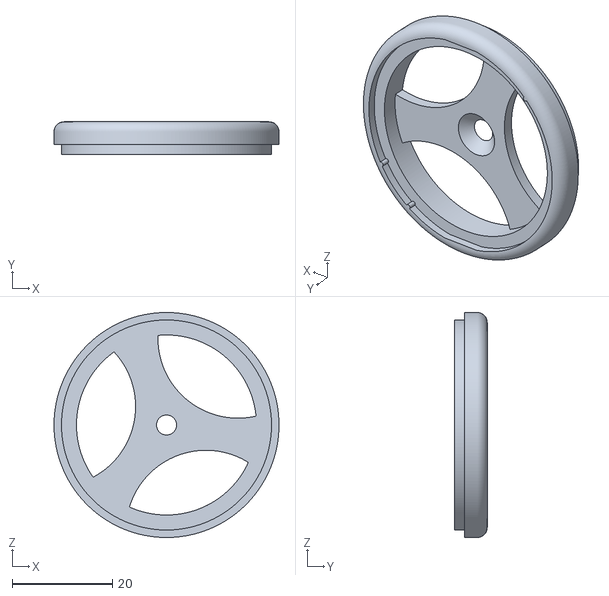
[picture p123: CAD file, 2022-05-02]
files/mods/trackpad/trackball-holder/top.stl
45.0 x 6.50 x 45.0
