Bastardkb/Charybdis/files/sensor_cover_v51.stl

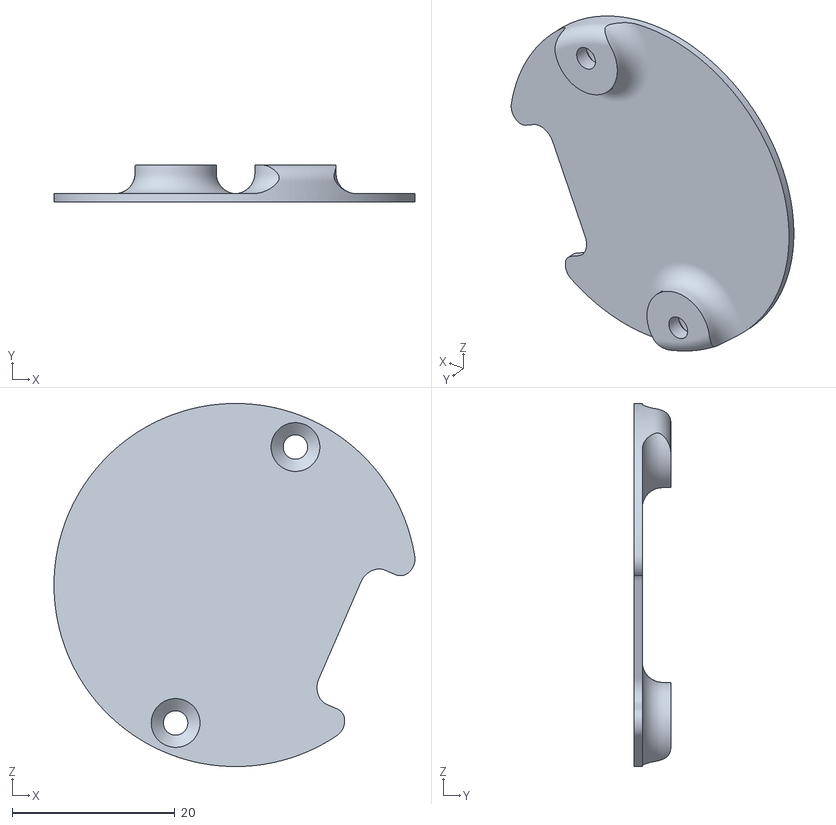
[picture p124: CAD file, 2021-08-09]
files/sensor_cover_v51.stl
44.4 x 4.50 x 44.7
