Bastardkb/Charybdis/files/3x5 nano/magnetic system/skeletyl plate.stl

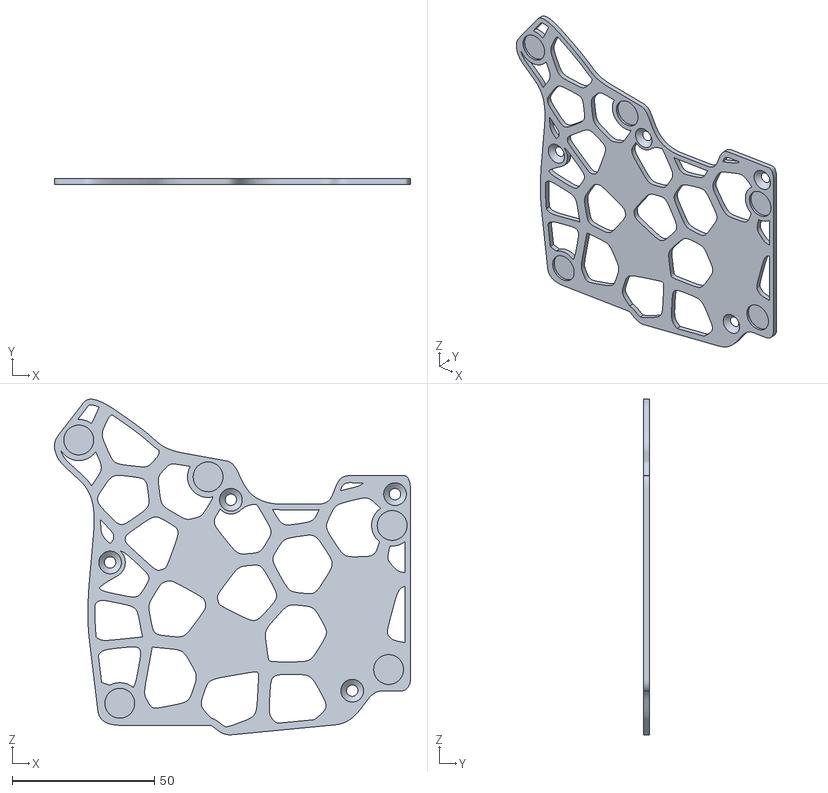
[picture p125: CAD file, 2026-03-30]
files/3x5 nano/magnetic system/skeletyl plate.stl
125.0 x 2.00 x 117.9
