Bastardkb/Charybdis/files/3x5 nano/plates/metal_magnet_v21.dxf

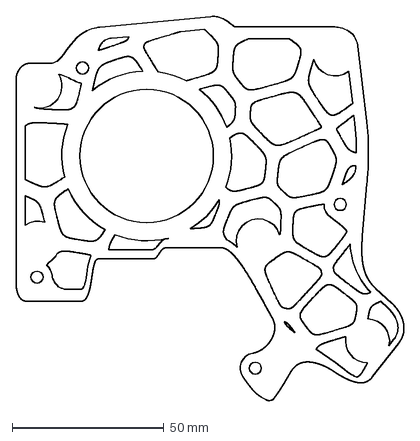
[picture p126: CAD file, 2023-03-13]
files/3x5 nano/plates/metal_magnet_v21.dxf
128.0 x 126.8 mm
