Bastardkb/Charybdis/files/3x5 nano/tent/alien/tent_v8_v41.3mf

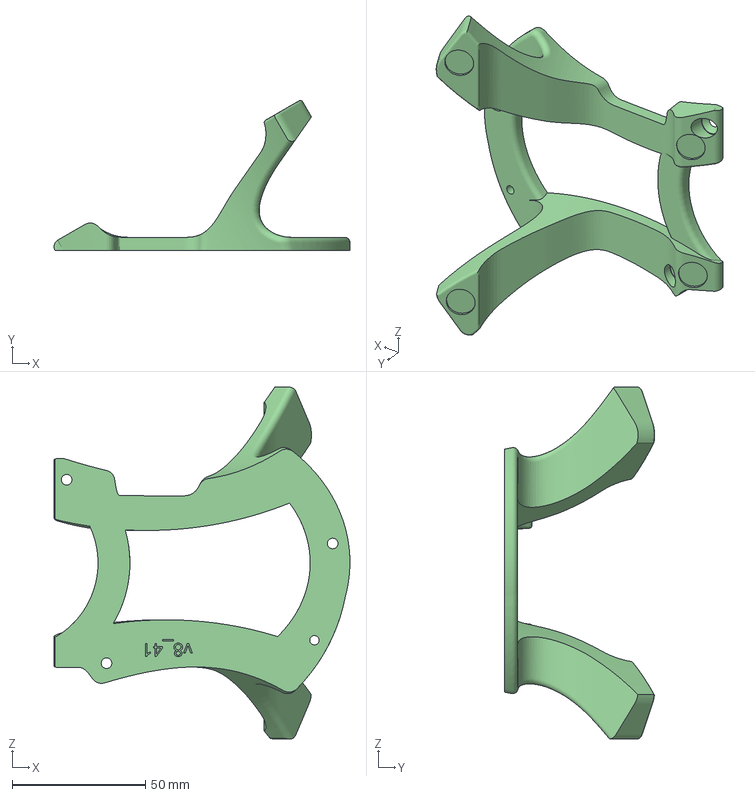
[picture p127: CAD file, 2024-06-24]
files/3x5 nano/tent/alien/tent_v8_v41.3mf
111.2 x 56.4 x 132.3 mm
