Bastardkb/Charybdis/files/3x5+3/LowTrackball/mcu_holder.stl

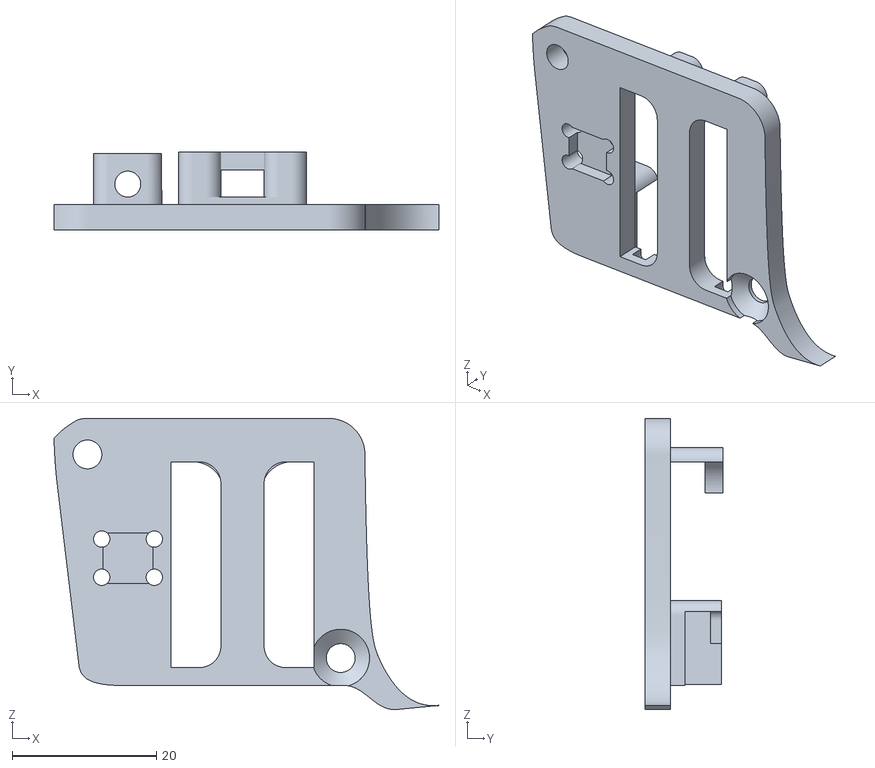
[picture p128: CAD file, 2023-08-22]
files/3x5+3/LowTrackball/mcu_holder.stl
53.4 x 10.9 x 40.4
