Bastardkb/Charybdis/files/3x5+3/MountedMods/TopTrackballCover v18.stl

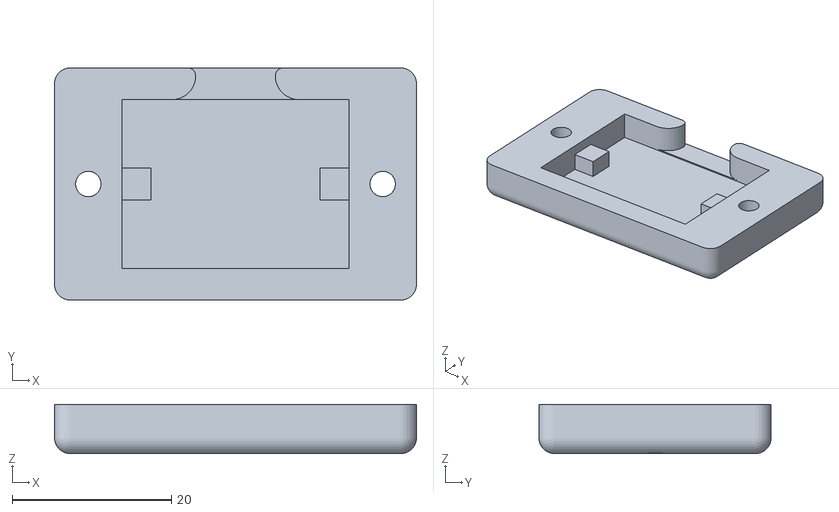
[picture p129: CAD file, 2022-09-18]
files/3x5+3/MountedMods/TopTrackballCover v18.stl
45.5 x 29.2 x 6.20
