Bastardkb/Charybdis/files/3x6 mini/tent_flush_v1_v5.stl

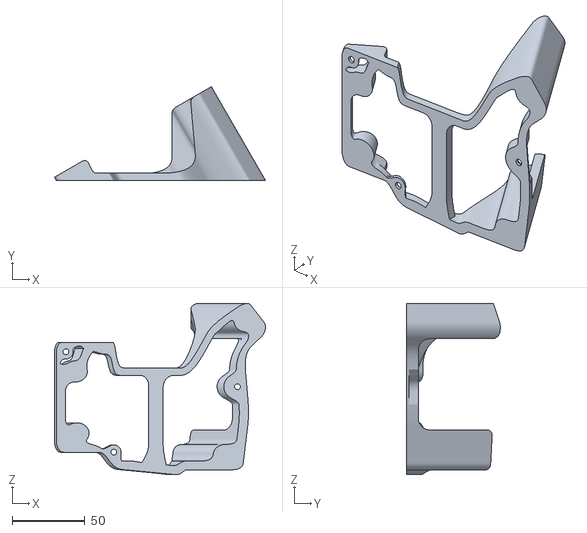
[picture p130: CAD file, 2025-03-21]
files/3x6 mini/tent_flush_v1_v5.stl
145.1 x 64.4 x 117.9
