Bastardkb/Charybdis/files/4x6/MK2/charybdis_v4_6_plate_L.stl

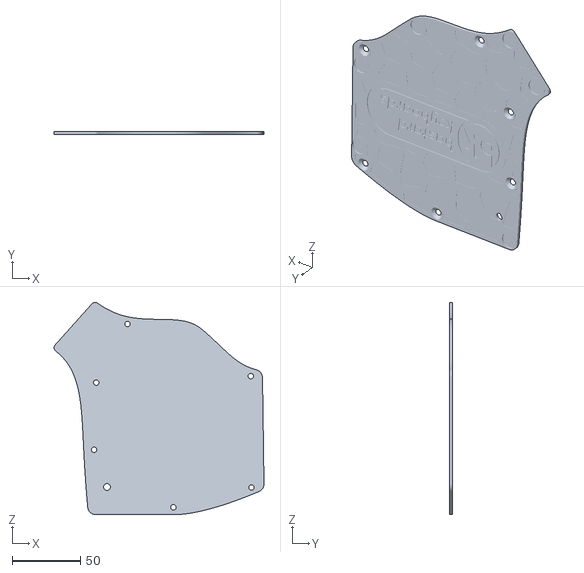
[picture p131: CAD file, 2025-06-26]
files/4x6/MK2/charybdis_v4_6_plate_L.stl
154.2 x 2.00 x 155.9
