Bastardkb/Charybdis/files/mods/modular-thumb-cluster/Track-Thumb.stl

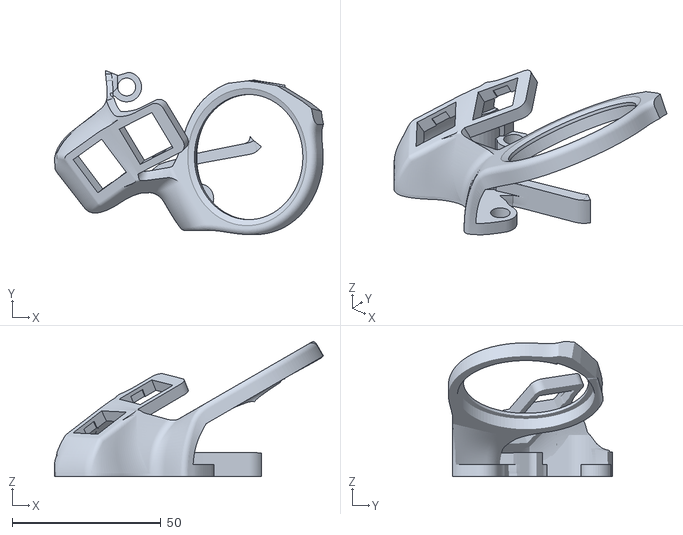
[picture p132: CAD file, 2022-09-18]
files/mods/modular-thumb-cluster/Track-Thumb.stl
90.3 x 55.1 x 45.4
