Bastardkb/Charybdis/files/mods/tenting-stand-with-wrist-pads/left-case-bottom-scylla.3mf

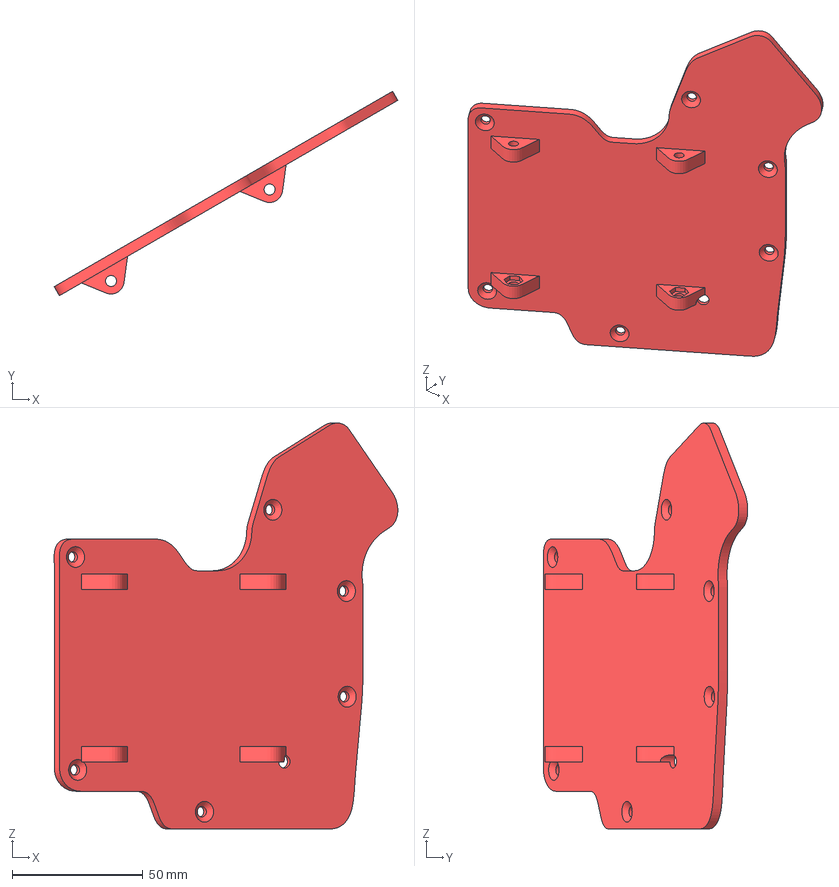
[picture p133: CAD file, 2022-11-10]
files/mods/tenting-stand-with-wrist-pads/left-case-bottom-scylla.3mf
131.4 x 78.2 x 155.3 mm
