Bastardkb/Charybdis/files/mods/tenting-stand-with-wrist-pads/wrist-pad-variant-parts/pads-arm-short-for-angled-base.3mf

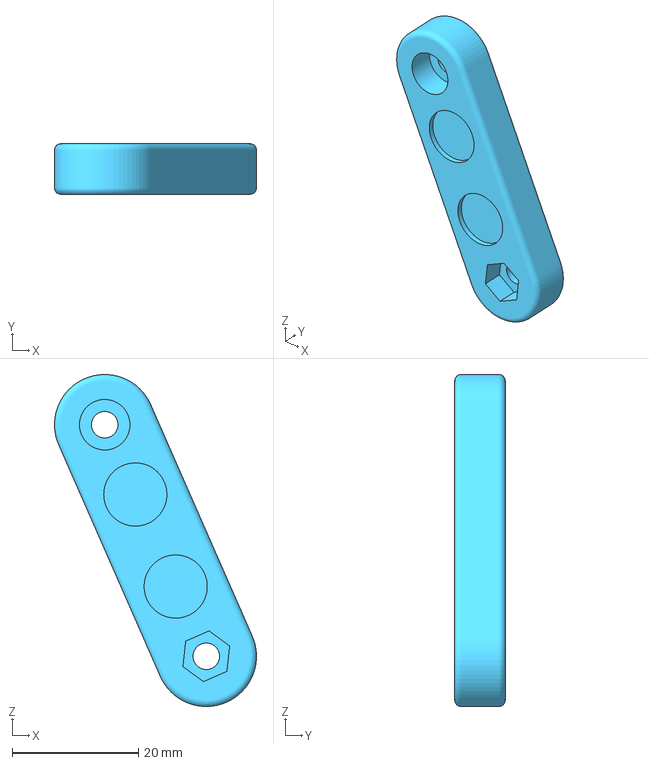
[picture p134: CAD file, 2023-03-06]
files/mods/tenting-stand-with-wrist-pads/wrist-pad-variant-parts/pads-arm-short-for-angled-base.3mf
32.0 x 8.00 x 52.5 mm
