Bastardkb/Charybdis/files/3x5 nano/plates/alien_v2_185.stl

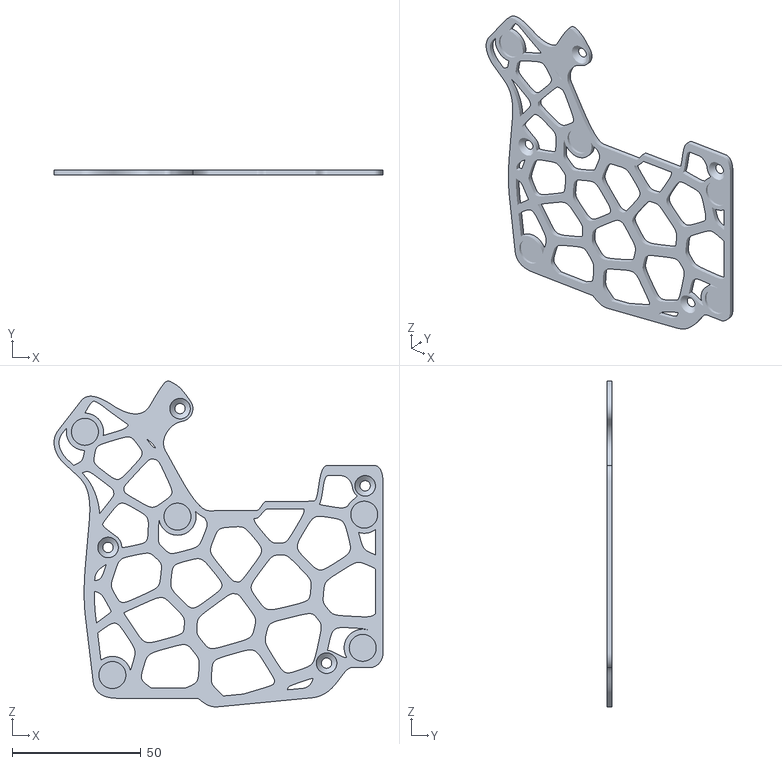
[picture p135: CAD file, 2022-06-07]
files/3x5 nano/plates/alien_v2_185.stl
128.0 x 2.00 x 126.7
