Bastardkb/Charybdis/files/3x5 nano/tent/alien/tent_v7_68.stl

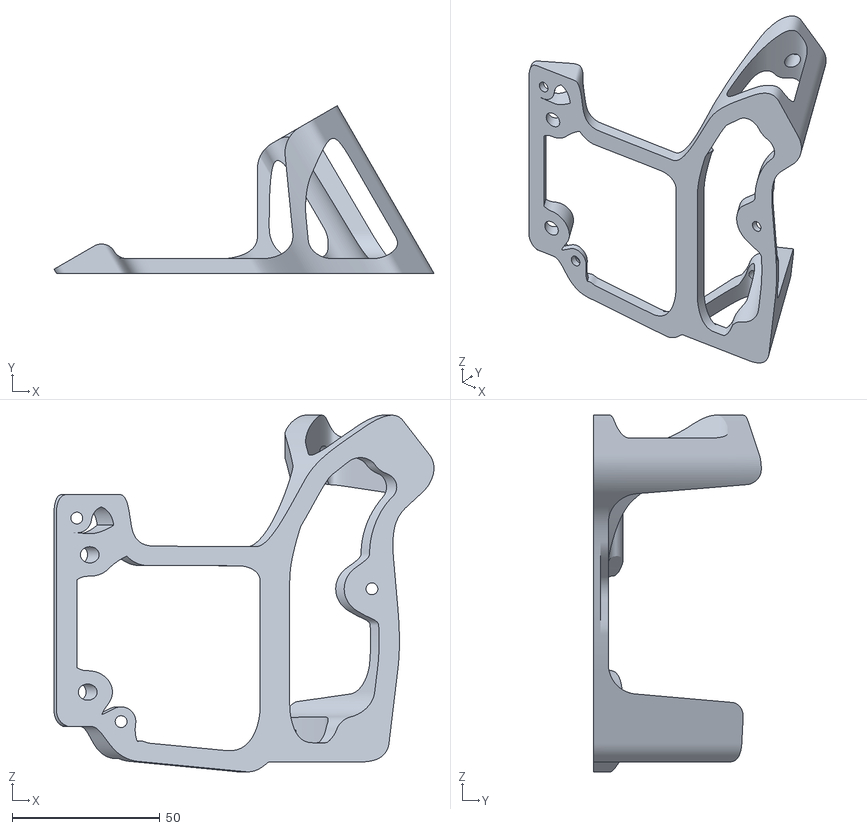
[picture p136: CAD file, 2022-06-09]
files/3x5 nano/tent/alien/tent_v7_68.stl
128.8 x 56.8 x 120.9
