Bastardkb/Charybdis/files/3x5+3/MountedMods/LargeKnobLowProBlank v3.stl

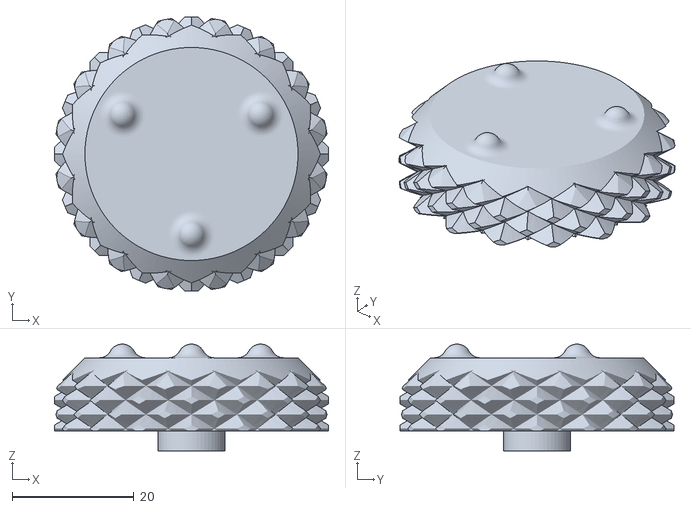
[picture p137: CAD file, 2022-09-18]
files/3x5+3/MountedMods/LargeKnobLowProBlank v3.stl
45.0 x 45.0 x 17.5
