Bastardkb/Charybdis/files/3x6 mini/CMini_v1_v11.step

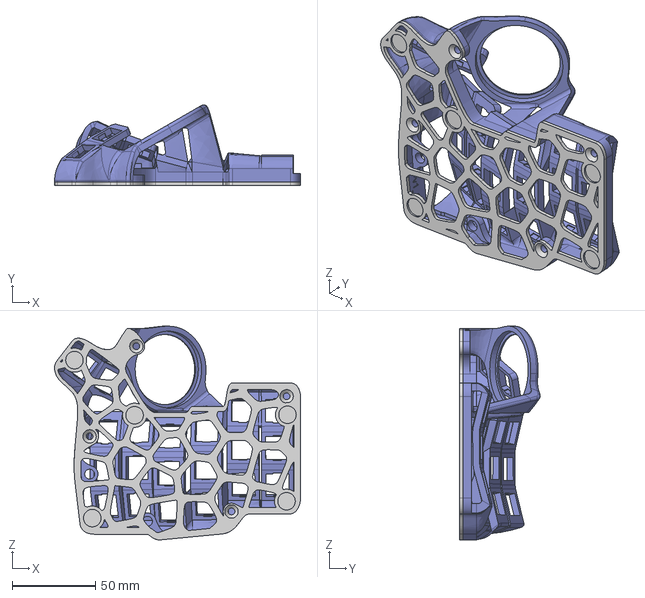
[picture p138: CAD file, 2023-10-10]
files/3x6 mini/CMini_v1_v11.step
147.4 x 48.2 x 128.1 mm
