Bastardkb/Charybdis/files/mods/modular-thumb-cluster/Reg-Thumb.stl

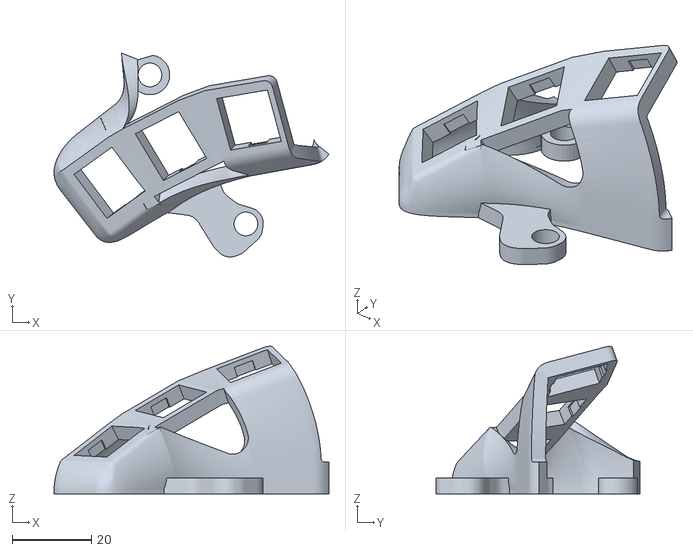
[picture p139: CAD file, 2022-09-18]
files/mods/modular-thumb-cluster/Reg-Thumb.stl
69.4 x 51.5 x 37.3
