Bastardkb/Charybdis/files/mods/tenting-stand-with-wrist-pads/plate.3mf

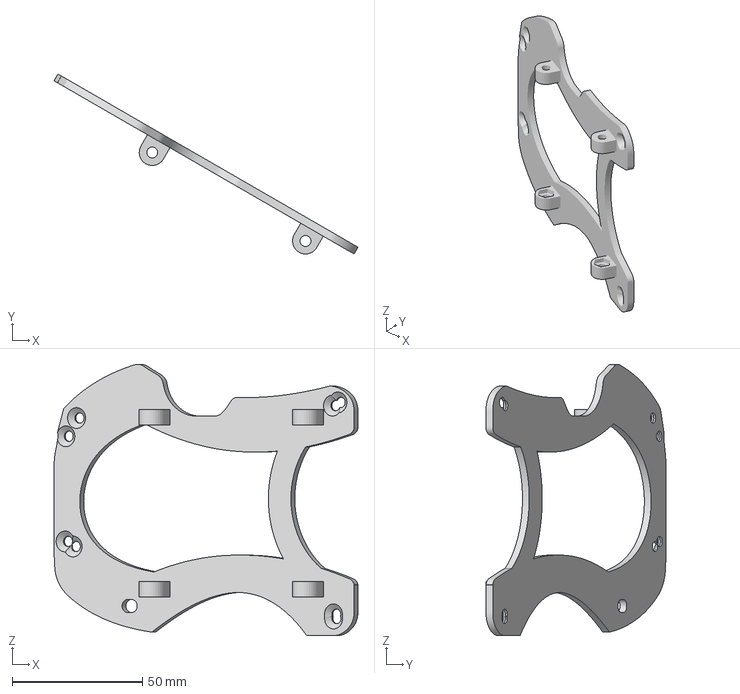
[picture p140: CAD file, 2022-11-07]
files/mods/tenting-stand-with-wrist-pads/plate.3mf
116.8 x 69.2 x 104.2 mm
