Bastardkb/Charybdis/files/mods/tenting-stand-with-wrist-pads/wrist-pad-variant-parts/pads-arm.3mf

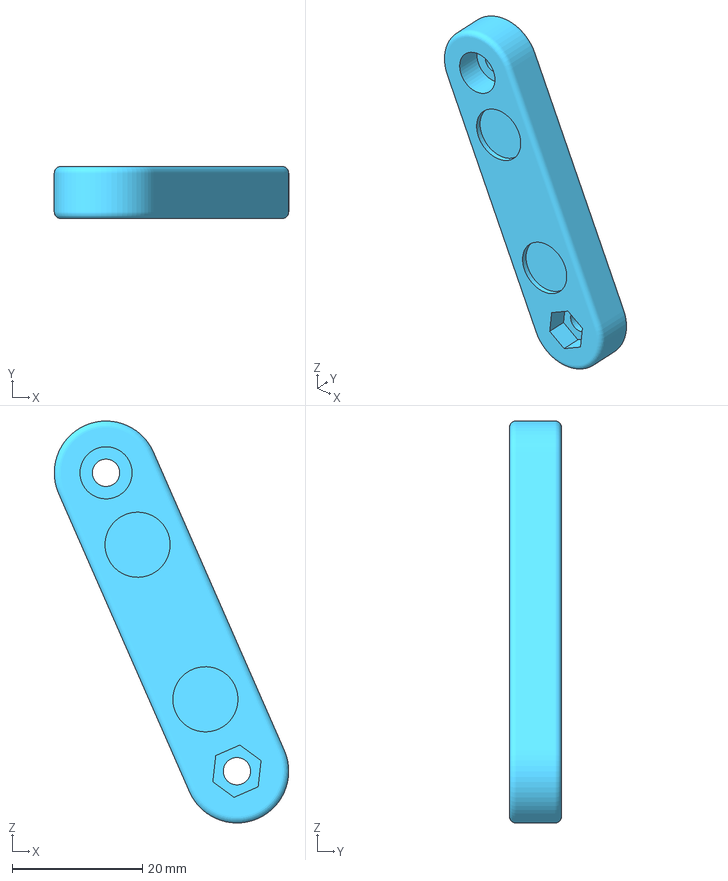
[picture p141: CAD file, 2022-11-07]
files/mods/tenting-stand-with-wrist-pads/wrist-pad-variant-parts/pads-arm.3mf
36.0 x 8.00 x 61.7 mm
