Bastardkb/Charybdis/files/3x5 nano/plates/plate_steel_cutting_hex.dxf

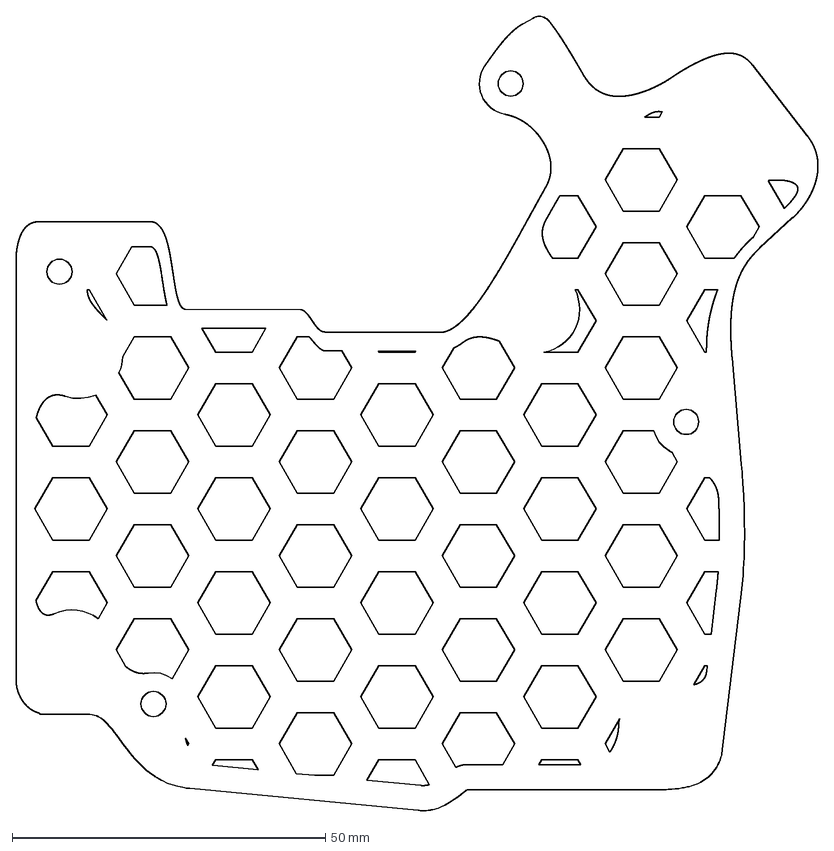
[picture p142: CAD file, 2022-03-21]
files/3x5 nano/plates/plate_steel_cutting_hex.dxf
128.0 x 126.8 mm
