Bastardkb/Charybdis/files/3x5 nano/tent/alien/tent15deg_v2_27.stl

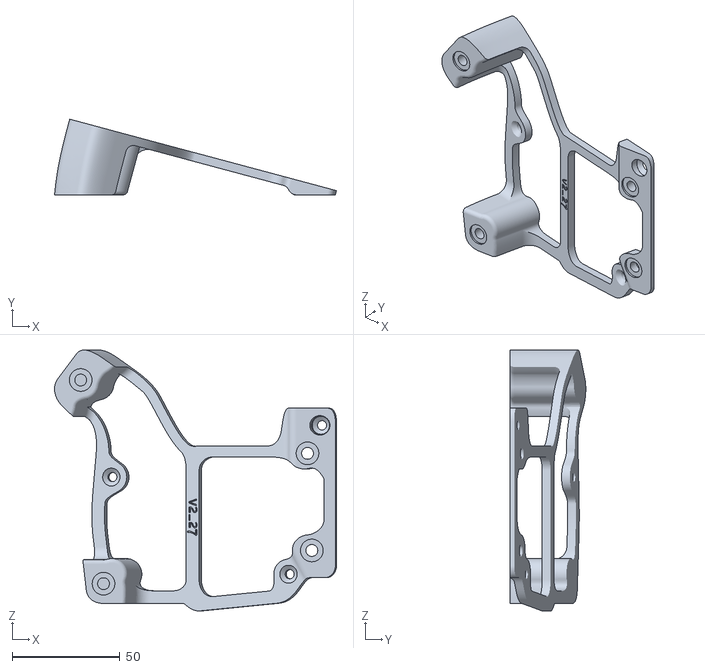
[picture p143: CAD file, 2022-06-09]
files/3x5 nano/tent/alien/tent15deg_v2_27.stl
130.6 x 35.0 x 120.9
