Bastardkb/Charybdis/files/3x5+3/MountedMods/TopTrackball30DegTentStand Cover v4.stl

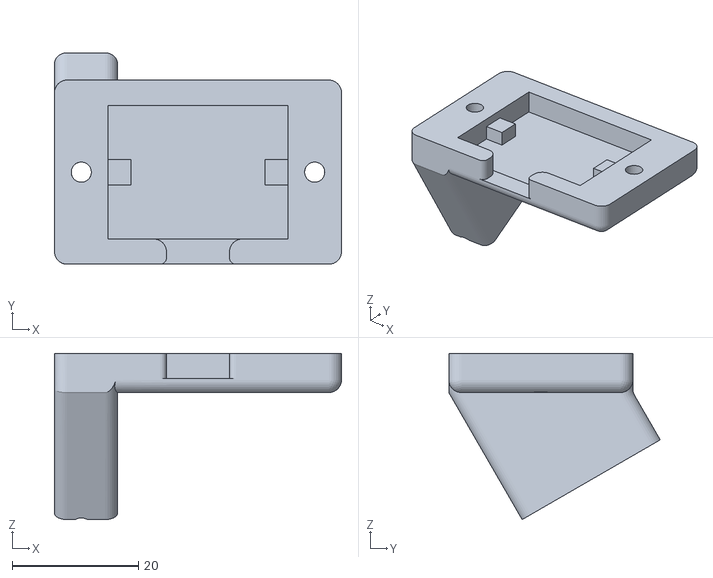
[picture p144: CAD file, 2022-09-18]
files/3x5+3/MountedMods/TopTrackball30DegTentStand Cover v4.stl
45.5 x 33.5 x 26.3
