Bastardkb/Charybdis/files/4x6/MK2/tent_alien_5deg_v27.stl

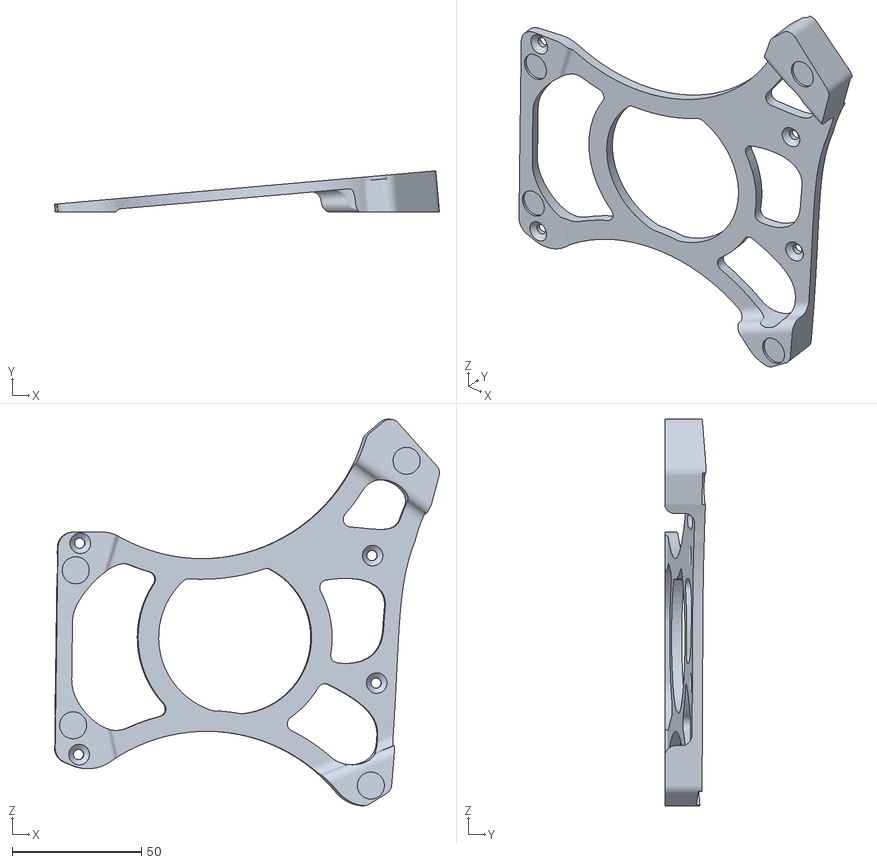
[picture p145: CAD file, 2025-01-17]
files/4x6/MK2/tent_alien_5deg_v27.stl
149.0 x 16.0 x 149.6
