Bastardkb/Charybdis/files/mods/tenting-stand-with-wrist-pads/bottom.3mf

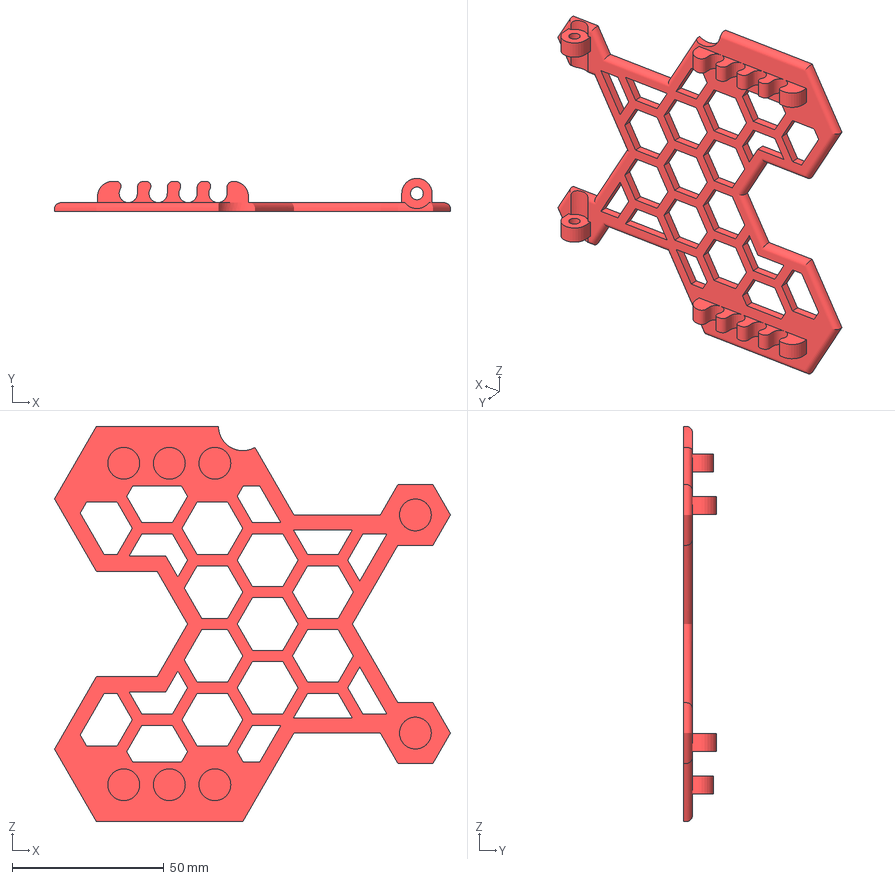
[picture p146: CAD file, 2022-11-07]
files/mods/tenting-stand-with-wrist-pads/bottom.3mf
130.3 x 11.0 x 130.1 mm
