Bastardkb/Charybdis/files/mods/tenting-stand-with-wrist-pads/wrist-pad-variant-parts/pads-base.3mf

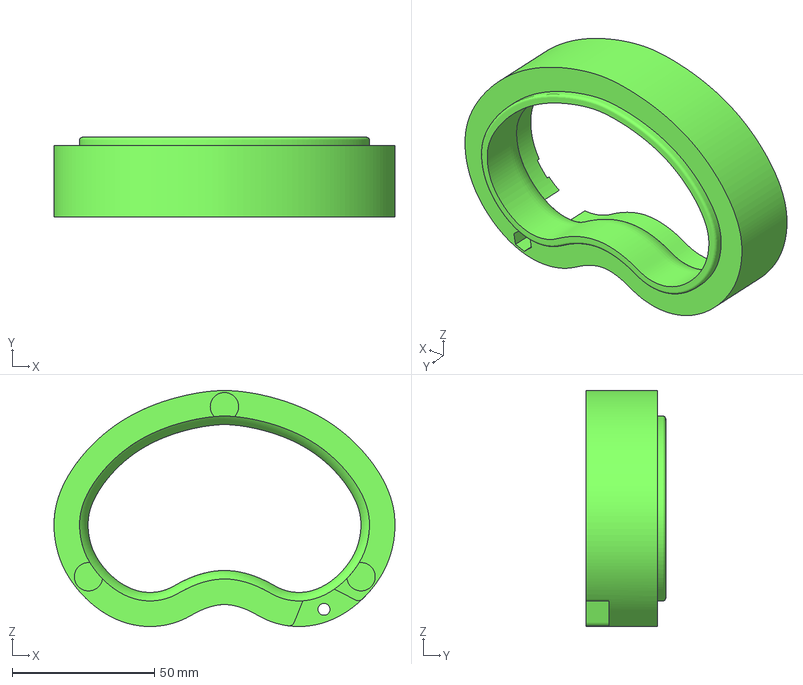
[picture p147: CAD file, 2022-11-07]
files/mods/tenting-stand-with-wrist-pads/wrist-pad-variant-parts/pads-base.3mf
120.0 x 28.0 x 83.1 mm
