Bastardkb/Charybdis/files/3x5 nano/plates/hex_v1_150.stl

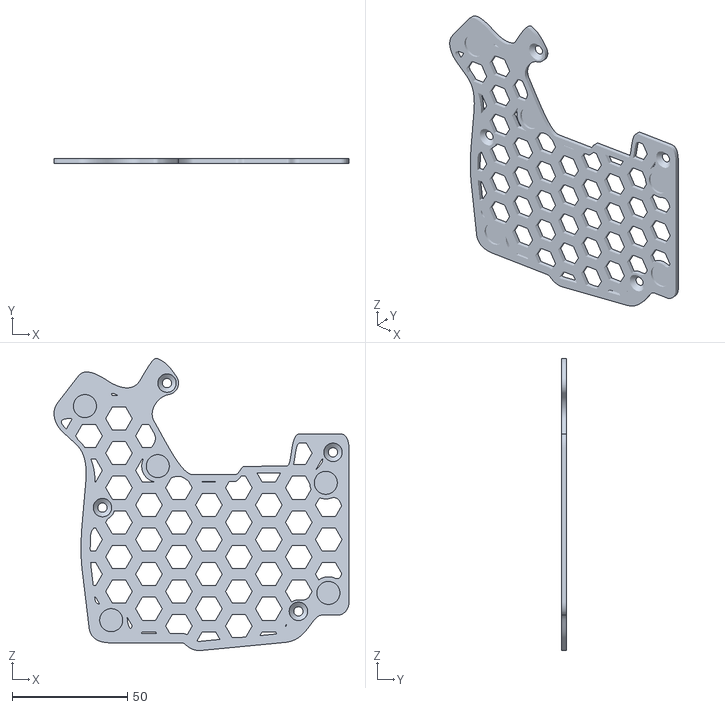
[picture p148: CAD file, 2021-08-06]
files/3x5 nano/plates/hex_v1_150.stl
128.0 x 2.00 x 126.7
