Bastardkb/Charybdis/files/3x5 nano/tent/alien/plate_voronoi_v1_5.stl

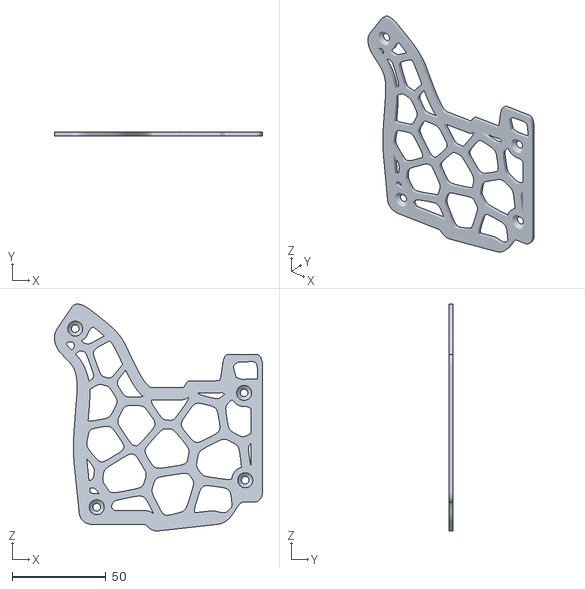
[picture p149: CAD file, 2022-05-12]
files/3x5 nano/tent/alien/plate_voronoi_v1_5.stl
110.8 x 2.00 x 120.9
