Bastardkb/Charybdis/files/3x5+3/MountedMods/Top57mmTrackball v5.stl

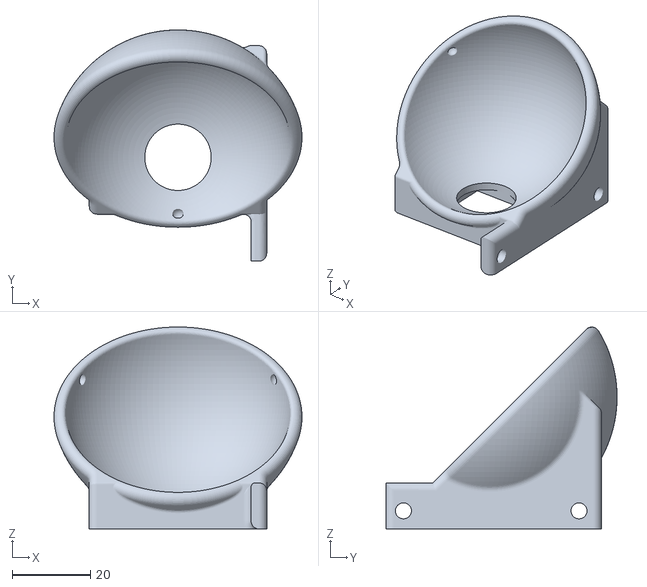
[picture p150: CAD file, 2022-09-18]
files/3x5+3/MountedMods/Top57mmTrackball v5.stl
63.6 x 59.2 x 51.7
