Bastardkb/Charybdis/files/4x6/MK2/charybdis_v4_247_right.stl

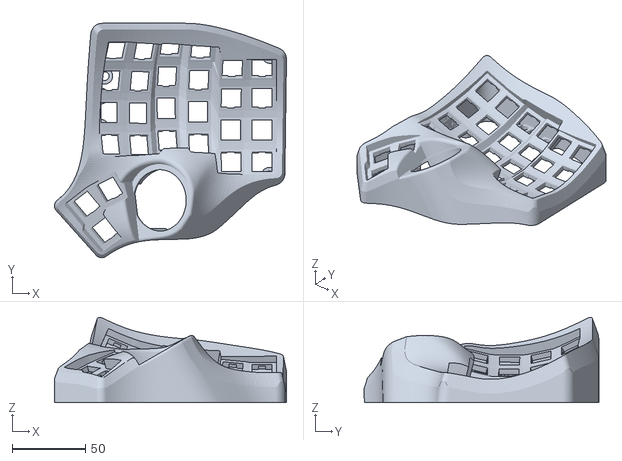
[picture p151: CAD file, 2024-12-30]
files/4x6/MK2/charybdis_v4_247_right.stl
158.2 x 159.9 x 58.1
