Bastardkb/Charybdis/files/mods/tenting-stand-with-wrist-pads/tenting-arm.3mf

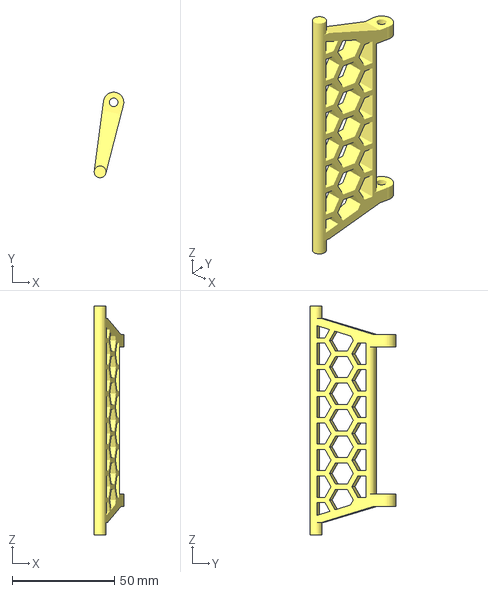
[picture p152: CAD file, 2022-11-07]
files/mods/tenting-stand-with-wrist-pads/tenting-arm.3mf
14.5 x 41.9 x 112.0 mm
