Bastardkb/Charybdis/files/mods/tenting-stand-with-wrist-pads/wrist-pad-variant-parts/bottom-with-pad-connector.3mf

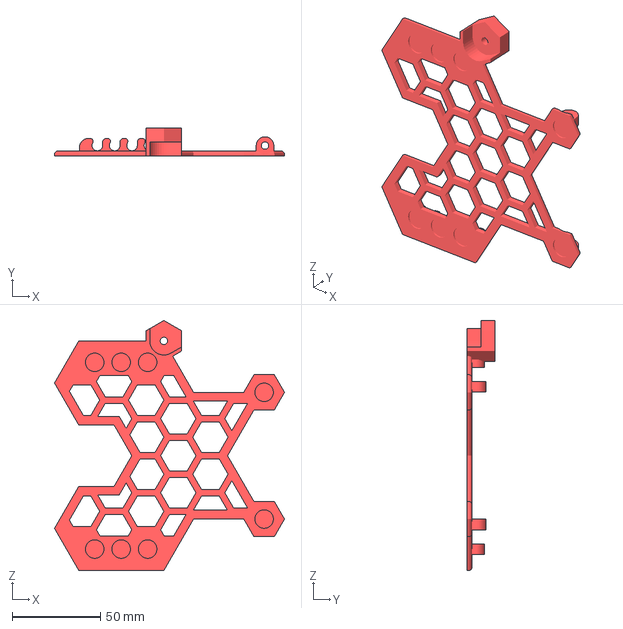
[picture p153: CAD file, 2022-11-07]
files/mods/tenting-stand-with-wrist-pads/wrist-pad-variant-parts/bottom-with-pad-connector.3mf
130.3 x 16.0 x 141.6 mm
