Bastardkb/Charybdis/files/3x5+3/MountedMods/LargeKnobLowProSierpinski v1.stl

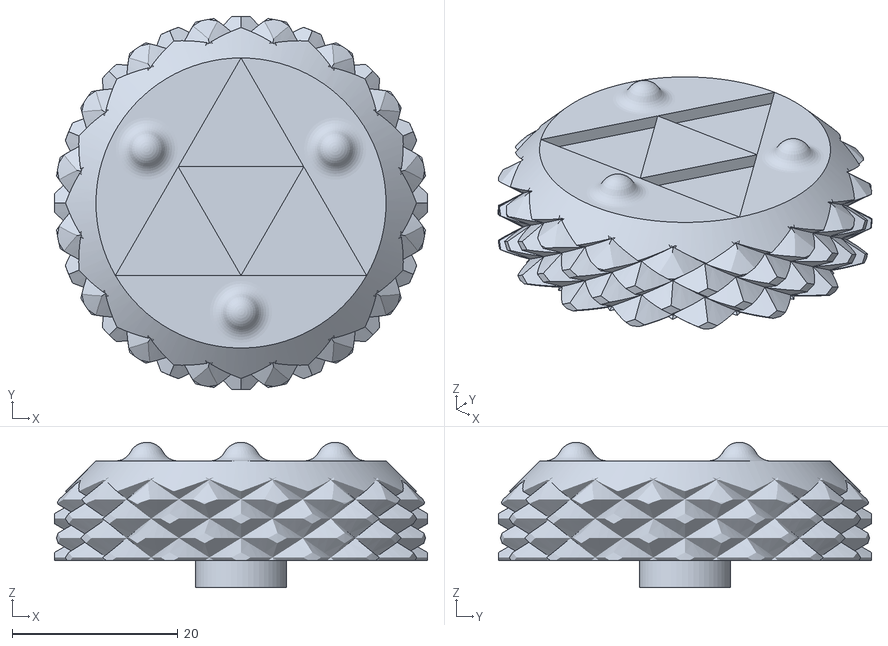
[picture p154: CAD file, 2022-09-18]
files/3x5+3/MountedMods/LargeKnobLowProSierpinski v1.stl
45.0 x 45.0 x 17.5
