Bastardkb/Charybdis/files/mods/tenting-stand-with-wrist-pads/wrist-pad-variant-parts/pads-optional-extension.3mf

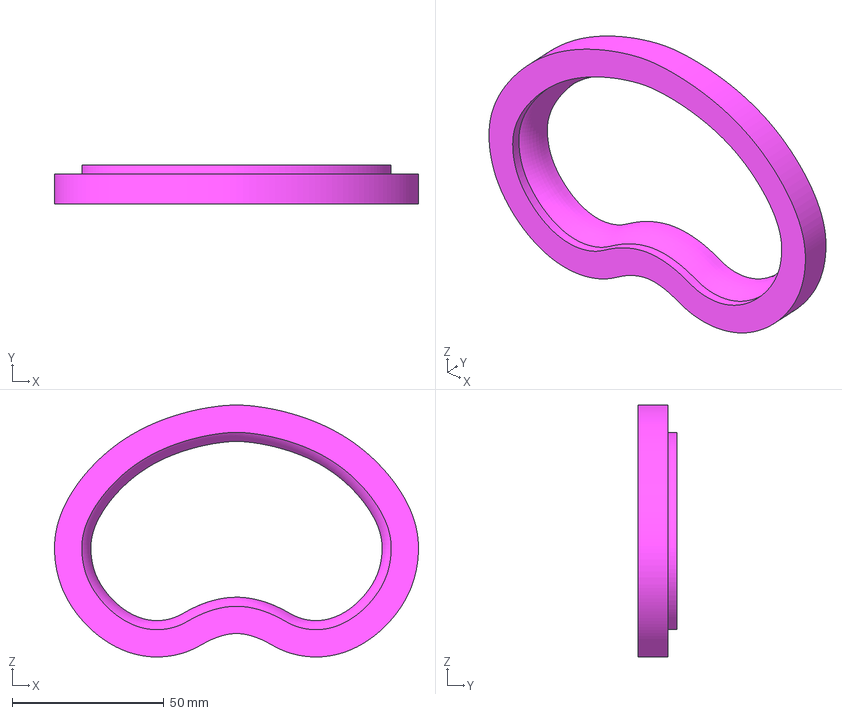
[picture p155: CAD file, 2022-11-07]
files/mods/tenting-stand-with-wrist-pads/wrist-pad-variant-parts/pads-optional-extension.3mf
120.0 x 13.0 x 83.0 mm
