Bastardkb/Charybdis/files/3x5+3/MountedMods/Top55mmTrackball v2.stl

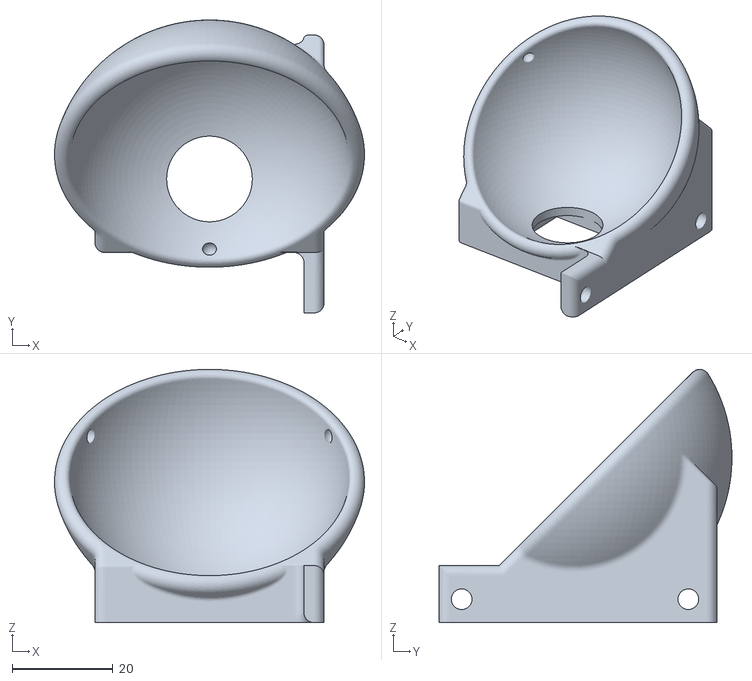
[picture p156: CAD file, 2022-09-18]
files/3x5+3/MountedMods/Top55mmTrackball v2.stl
61.5 x 58.2 x 50.3
