Bastardkb/Charybdis/files/mods/tenting-stand-with-wrist-pads/wrist-pad-variant-parts/pads-holder.3mf

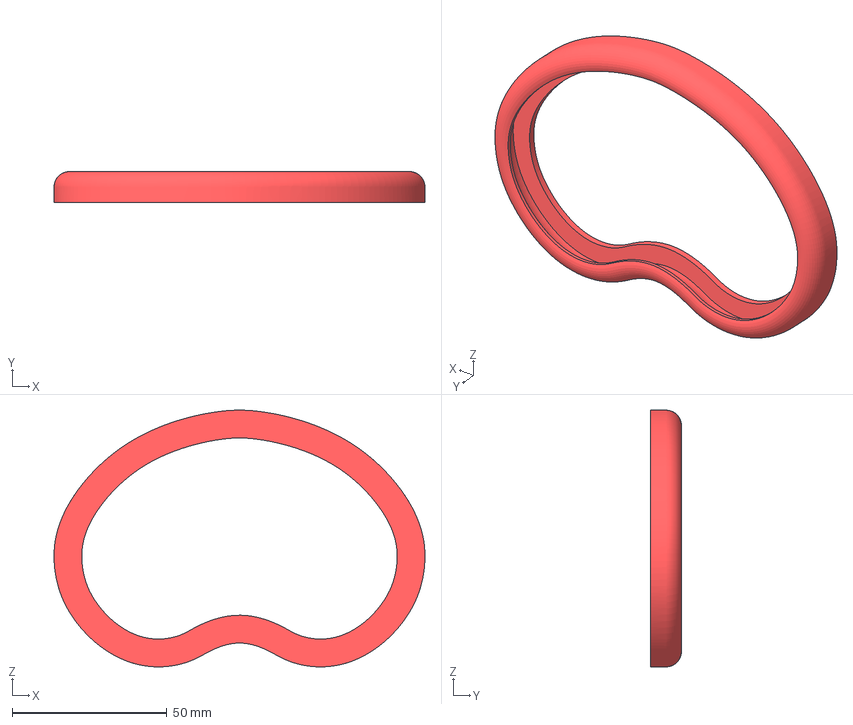
[picture p157: CAD file, 2022-11-07]
files/mods/tenting-stand-with-wrist-pads/wrist-pad-variant-parts/pads-holder.3mf
120.0 x 10.0 x 83.0 mm
