Bastardkb/Charybdis/files/3x5+3/MountedMods/3x5+3 V4T02 v11.stl

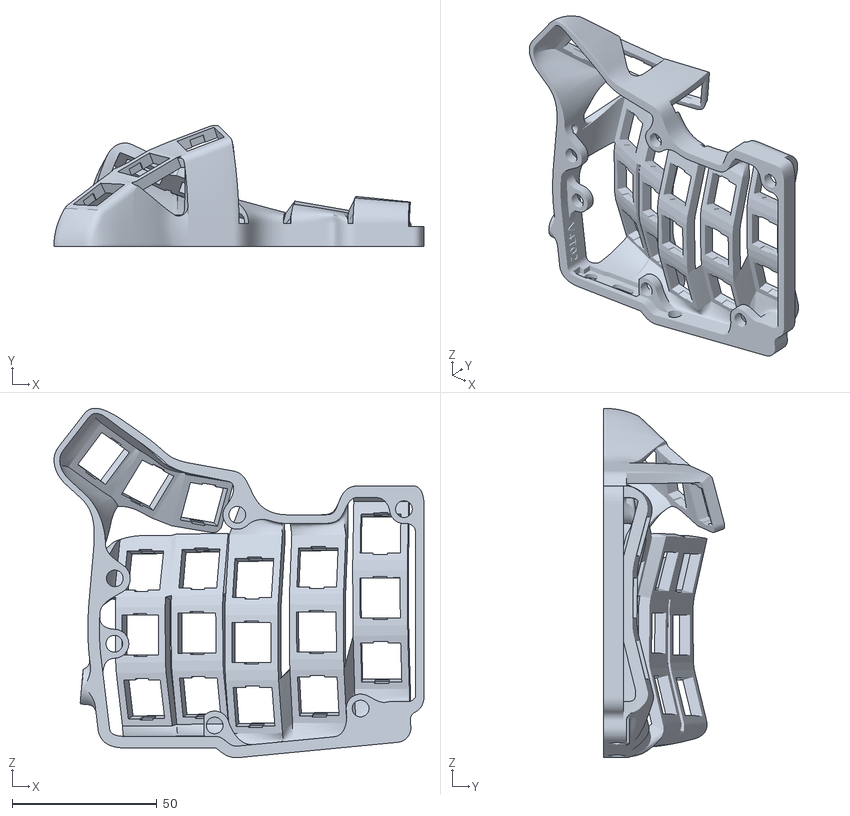
[picture p158: CAD file, 2022-09-18]
files/3x5+3/MountedMods/3x5+3 V4T02 v11.stl
128.0 x 42.0 x 120.9
